zeuscs09/perch/firmware/main/pch_props.h

// Prop — ของที่มาสคอตถือหรือลอยเหนือหัว บอกว่ากำลังทำอะไร
// พอร์ตจาก tools/gen/props.py แบบตรงตัว (ตัวเลขต้องตรงกัน ไม่งั้น preview โกหก)
#pragma once

#include "pch_rects.h"

typedef enum {
    PCH_PROP_NONE = 0,
    PCH_PROP_MAGNIFIER,
    PCH_PROP_LAPTOP,
    PCH_PROP_HAMMER,
    PCH_PROP_GLOBE,
    PCH_PROP_DOTS,
    PCH_PROP_BANG,
    PCH_PROP_CLOCK,
    PCH_PROP_ZZZ,
    PCH_PROP_SPARKLE,
    PCH_PROP_CREW,
    PCH_PROP_BEACON,
} pch_prop_t;

#define PCH_HEAD_CX 8.0f  // กึ่งกลางลำตัวในแนวนอน
#define PCH_HAND_X 17.0f  // ขอบซ้ายของพื้นที่ prop ที่ถือ (แขนจบที่ 16.25)
#define PCH_HAND_Y 3.0f  // = ขอบบนของแขน (NUB_Y ใน pch_mascot.c)

// ตาข้างขวา — อยู่ที่นี่เพราะ prop บางชิ้น (แว่นขยาย) ต้องเล็งไปที่ตา
// pch_mascot.c ใช้ค่าชุดเดียวกันนี้ ไม่ต้องซิงก์สองที่
// ตากว้างหนึ่งช่องตาราง (1.5) อยู่ช่องที่ 6 ของลำตัวและต่ำจากยอดหัวหนึ่งช่อง — ตามภาพอ้างอิง
#define PCH_EYE_R 11.0f
#define PCH_EYE_Y 1.5f
#define PCH_EYE_S 1.5f
// ตาที่อยู่หลังเลนส์ต้องโตกว่าอีกข้าง ไม่งั้นวงแหวนอ่านเป็นแค่ห่วงคล้องหน้า ไม่ใช่แว่นขยาย
// pch_mascot.c เป็นคนวาดตาที่ขยายแล้ว (มันรู้ว่าตากำลังเป็นท่าไหน เช่นตอนกะพริบ)
#define PCH_EYE_MAG 2.0f

// แล็ปท็อป — วางหน้าลำตัว ไม่ใช่ช่อง prop ข้างตัว จึงมีค่าคงที่ชุดของตัวเอง
// ใหญ่เกือบเท่าลำตัว แต่แคบกว่าอยู่ราวข้างละ 1 unit — ช่องนั้นคือที่ที่ไหล่ยังโผล่ให้เห็น
// แขนที่โผล่ข้างฝาคือแขนเดิมของลำตัว (nub) ที่ขยับขึ้นลง — ไม่มีแขนวาดเพิ่มพาดหน้าฝา
#define PCH_LID_X 3.25f  // ลำตัวกิน 2..14 — เหลือไหล่โผล่ข้างละ 1.25
#define PCH_LID_W 9.5f
#define PCH_LID_Y 4.5f   // ขอบบนต่ำกว่าตา (จบที่ 3.0) — จอไม่บังหน้า
#define PCH_LID_H 6.2f
#define PCH_LAP_X 2.55f  // ฐาน — ยื่นออกกว่าฝาจอนิดเดียว จึงอ่านเป็นแล็ปท็อปไม่ใช่ป้าย
#define PCH_LAP_W 10.9f
#define PCH_LAP_Y 10.7f  // ฐานจบพอดีระดับฝ่าเท้า (12.0) — แล็ปท็อปบังขาหมดทั้งสี่
#define PCH_LAP_H 1.3f

// ฟองข้อความเหนือหัว — thinking
#define PCH_BUB_W 9.4f
#define PCH_BUB_H 3.9f

// เลนส์ยังต้องใหญ่กว่าหัวและล้นขึ้นไปด้านบนเหมือนเดิม แต่หัวแคบลงตอนแก้สัดส่วน
// 6.0 คือค่าที่รูในวง (4.5) ยังกินตาที่ขยายแล้ว (1.5 x 2 = 3.0) ได้สบาย
// ทั้งคู่ต้องลงตารางพิกเซล (ทวีคูณของ 0.25) รวมถึงมุมที่ตัด s/4 = 1.5 และ s/4 - t = 0.75
// ด้วย: กระจกกับวงแหวนไล่บันไดมุมคนละชุด ถ้าค่าไหนตกครึ่งพิกเซล บันไดจะเหลื่อมกัน
#define PCH_LENS_S 6.0f   // ขนาดเลนส์แว่นขยาย
#define PCH_LENS_T 0.75f  // ความหนาของขอบเลนส์

// แว่นตา — ท่านั่งพิมพ์ (writing) ไม่ใช่ pch_prop_t เพราะติดหน้าไปกับตา
// ต้องยุบและเลื่อนไปพร้อมตาทุกเฟรม (pch_mascot.c จึงวาดมันในชุดเดียวกับตา ไม่ใช่ชุด prop)
// ทุกค่าลงตาราง 0.25 unit (= 1 px) รวมมุมที่ตัด s/4 = 0.75 และ s/4 - t = 0.25
#define PCH_GLS_S 3.0f
#define PCH_GLS_T 0.5f
// ขาแว่นยาวเท่าที่พอไปจบพอดีขอบลำตัว (2.0 และ 14.0) — เลยออกไปจะอ่านเป็นเส้นลอยข้างหัว
#define PCH_GLS_TEMPLE 0.75f

// ค้อน + หมวกวิศวกร + แท่นเหล็ก — ทั้งชุดคือ prop เดียวกัน (Bash) จึงใช้ค่าคงที่ร่วมกัน
// หนึ่งลูปคือการทุบหนึ่งครั้งที่มีจังหวะเงื้อนำ ไม่ใช่ค้อนเด้งขึ้นลงสองรอบ:
// จังหวะเงื้อคือสิ่งที่ทำให้การกระแทกมีน้ำหนัก ถ้าตัดทิ้งจะเหลือแค่ของขยับไปมา
typedef enum { PCH_HAM_READY, PCH_HAM_WINDUP, PCH_HAM_STRIKE, PCH_HAM_RECOVER } pch_ham_stage_t;
// ขอบเขตของแต่ละท่าในลูป — ท่าฟาดสั้นที่สุด (สองเฟรม) เพราะการกระแทกต้องคม
#define PCH_HAM_T_WINDUP 0.25f
#define PCH_HAM_T_STRIKE 0.45f
#define PCH_HAM_T_RECOVER 0.62f

#define PCH_ANVIL_CX 20.0f  // กลางแท่น = ปลายทางที่หัวค้อนตกลงมา
#define PCH_ANVIL_TOP 9.5f  // ผิวบนของบล็อก = ก้นของชิ้นงานร้อน ทั้งตอนยุบและไม่ยุบ
#define PCH_HOT_UP_H 1.3f   // ชิ้นงานยุบลงราวครึ่งหนึ่งตอนโดนทุบ
#define PCH_HOT_DOWN_H 0.7f

#define PCH_HAM_HEAD_W 4.0f  // หัวค้อน
#define PCH_HAM_HEAD_H 2.4f
#define PCH_HAM_GRIP_W 1.4f  // ความหนาของด้าม
#define PCH_HAM_STEP 0.65f  // ระยะไล่ของบล็อกด้ามต่อชิ้น ทั้งสองแกน = ทแยง 45 องศาพอดี
#define PCH_HAM_BLK 1.4f  // ด้านของบล็อกด้าม — ใหญ่กว่า step จึงเหลื่อมกันเป็นเส้นทึบ
#define PCH_HAM_N 5  // จำนวนบล็อกด้าม

void pch_prop_build(pch_rects_t *out, pch_prop_t prop, float phase, bool connected);

// กระจกในเลนส์แว่นขยาย — ต้องวาดก่อนตา จึงแยกออกจาก pch_prop_build() ที่วาดหลังตา
void pch_prop_magnifier_glass(pch_rects_t *out, float phase, bool connected);

// แว่นตาคร่อมตาสองข้าง — วาดหลังตาในชุดเดียวกับตา จึงแยกออกจาก pch_prop_build()
void pch_prop_glasses(pch_rects_t *out, float eye_l, bool connected);

// แท่นเหล็กที่ค้อนทุบ — วางอยู่กับพื้น จึงแยกจาก pch_prop_build() ที่ถูกเลื่อนตามตัวมาสคอต
void pch_prop_hammer_anvil(pch_rects_t *out, float phase, bool connected);

// ท่าของการทุบในเฟรมนี้ — pch_mascot.c ใช้กำหนดท่าตัวมาสคอตให้ตรงจังหวะกับค้อน
pch_ham_stage_t pch_prop_hammer_stage(float phase);
