zeuscs09/perch/firmware/main/pch_face.h

// โหมดทดลอง — ใบหน้าที่ขยับปากตามความดังเสียง (พอร์ตจาก Berlin บนเว็บ)
//
// ตอบคำถามเดียว: **ปากที่ขยับตามเสียงดูดีพอบนจอ 2.8 นิ้วไหม** ก่อนจะลงเงินซื้อบอร์ด
// ที่มีไมค์กับ codec — ยังไม่มีระบบเสียงในโหมดนี้ ใช้เส้นความดังที่อัดไว้ล่วงหน้าแทน
//
// กลไกปากมาจาก frontend/js/avatar.js ของ Berlin ตรงๆ:
//     mouthScaleY = 0.25 + speechAmp * 3.6
//     speechAmp   = lerp(speechAmp, target, 0.24)
// ไม่มี viseme ไม่มีการวิเคราะห์เสียงพูด — ความสูงของช่องปากผูกกับความดังตัวเดียว
#pragma once

// วาดหน้าแล้ววนเล่นเส้นเสียงไปเรื่อยๆ ไม่คืนค่า
void pch_face_run(void);
