zeuscs09/perch/firmware/main/pch_face_env.h

// เส้นความดังจากเสียงพูดจริง (macOS say -v Kanya, ไทย) ที่ 30 fps
// สร้างด้วย tools/make_envelope.py — ฝังไว้เพื่อทดสอบการขยับปากโดยยังไม่ต้องมีระบบเสียง
#pragma once
#include <stdint.h>

#define PCH_ENV_FPS 30
#define PCH_ENV_LEN 181

static const uint8_t PCH_ENV[PCH_ENV_LEN] = {
      2,   2,   3,   4, 113, 160, 158, 157, 160, 139, 129,  73,   5,   0,  26,  96,
    169, 200, 198, 198, 178,  69,   0,  10,  16,  68, 141, 130, 126, 103,  52,   1,
      0,   0,   0,   0,   0,   9, 123, 149, 183, 196, 179, 207, 212, 214, 175, 136,
    201, 197, 195, 184, 115,   3,   0, 102, 159, 154, 159, 156, 214, 221, 213,  91,
     91, 147, 146, 140, 102,   6,   1,   7,   3,   2,  43, 179, 162, 146, 130, 117,
    122, 113, 118, 109, 105,  54,   5,   0,   0,   0,   0,   0,   0,  11,  18, 125,
    147, 139, 117,  35,   0,   0,  12,  26, 175, 198, 190, 176, 180, 243, 255, 250,
    240, 239, 232, 211, 192, 181, 175, 170, 164, 124,  26,   0,   0,   0,   0,   0,
      0, 116, 241, 253, 249, 248, 220, 145,  31,  86, 149, 136,  33, 103, 157, 152,
    147, 151, 173, 173, 146,  66, 108, 182, 178, 180, 174, 118,  31,  29,  21, 112,
    184, 192, 195, 186, 188, 206, 229, 225, 147, 134, 136,  89,   7,   3,   7,  27,
    128, 137, 127, 109,  70,
};
