zeuscs09/perch/firmware/main/pch_led.h

// RGB LED บนบอร์ด — ไฟบอกสถานะที่อ่านได้จากหางตา
//
// จอตอบว่า "เกิดอะไรขึ้นบ้าง" ซึ่งต้องหันไปอ่าน ส่วนไฟตอบคำถามเดียว:
// "ต้องลุกไปทำอะไรไหม" คำถามนั้นต้องตอบได้โดยไม่ต้องหันหน้า ไฟจึงไม่พยายาม
// บอกอะไรมากกว่าหนึ่งอย่าง
//
// ใช้ PWM ไม่ใช่เปิด/ปิดล้วน — เปิด/ปิดได้แค่ 7 สีและกะพริบแข็งๆ ซึ่งบนโต๊ะทำงาน
// อ่านเป็นสัญญาณเตือนตลอดเวลา ส่วนการหายใจช้าๆ อยู่ร่วมกับคนได้ทั้งวัน
#pragma once

#include <stdbool.h>

#include "pch_model.h"

void pch_led_init(void);

// กลางคืน = ดับสนิท ไม่ว่าสถานะจะเป็นอะไร
//
// เหตุผลที่ไฟดวงนี้มีอยู่คือ "บอกว่ามีคนรอเราตอบ" ซึ่งเป็นข้อความที่ส่งถึงคนที่ทำงานอยู่
// คนที่นอนอยู่ข้างๆ ไม่ได้เป็นผู้รับ ไฟส้มที่เต้นทุก 1.4 วินาทีข้างหัวเตียงจึงไม่ใช่
// สัญญาณอีกต่อไป มันคือสิ่งรบกวน
void pch_led_set_night(bool on);

// บอกไฟว่าภาพรวมตอนนี้เป็นยังไง — เรียกทุกครั้งที่ snapshot เปลี่ยน
// ไม่ต่อลิงก์ = ดับ (ไฟที่ยังสวยอยู่ตอนขาดการติดต่อคือการโกหก)
void pch_led_apply(const pch_snapshot_t *snap, bool connected);

// เดินจังหวะหายใจ เรียกจากลูปหลักพร้อมเวลาที่ผ่านไป (ms)
void pch_led_tick(int elapsed_ms);
