zeuscs09/perch/firmware/main/pch_night.h

// โหมดกลางคืน — จอเหลือแค่นาฬิกา ไฟดับ ไม่เตือนอะไรทั้งนั้น
//
// สำหรับเครื่องที่วางอยู่ในห้องนอน ซึ่งเปลี่ยนความหมายของทุกอย่างบนจอ:
// ตอนกลางวันมันคือแดชบอร์ดที่ควรเรียกร้องความสนใจเมื่อมีเรื่อง ตอนกลางคืนคนที่อยู่
// ในห้องไม่ได้จะลุกไปแก้อะไร การเตือนจึงไม่ได้ช่วยใคร มีแต่ปลุกคนให้ตื่น
//
// ## ทำไมถึงตัดทั้งจอ ไม่ใช่แค่หรี่ไฟหลัง
//
// จอ 320x240 ที่มีท้องฟ้าเต็มผืนกับมาสคอตสีชมพูสามตัว ปล่อยแสงออกมามากกว่าตัวเลข
// นาฬิกาบนพื้นดำหลายเท่า ต่อให้ไฟหลังเท่ากัน — ความสว่างที่ตาเห็นมาจาก *จำนวนพิกเซล
// ที่ติด* ไม่ใช่แค่กำลังไฟหลัง การหรี่อย่างเดียวจึงไม่พอสำหรับห้องมืด
#pragma once

#include <stdbool.h>

// เวลาปัจจุบันจาก snapshot ("HH:MM") — ตัวเดียวที่บอกบอร์ดว่าตอนนี้กี่โมง
// บอร์ดไม่มีนาฬิกาจริงของตัวเอง เวลาจึงมาพร้อมข้อมูลเสมอ
void pch_night_set_clock(const char *hhmm);

// ผู้ใช้แตะจอ — ออกจากโหมดกลางคืนชั่วคราว แล้วกลับเข้าเอง
void pch_night_wake(void);

void pch_night_tick(int elapsed_ms);

// อยู่ในโหมดกลางคืนอยู่ไหม (กลางคืน *และ* ไม่ได้เพิ่งถูกแตะ)
bool pch_night_active(void);
