zeuscs09/perch/firmware/main/pch_ui.c

#include "pch_ui.h"

#include <math.h>
#include <stdio.h>
#include <string.h>

#include "pch_mascot.h"
#include "pch_rects.h"
#include "layout.h"
#include "lvgl.h"

// ความสูง/ระยะของการ์ด — ตรงกับ tools/gen/screen.py
#define CARD_H 36
#define CARD_GAP 4

// หนึ่งลูปอนิเมชันยาวเท่าไร (ms) — ตรงกับสมมติฐาน "ลูปหนึ่งราว 1 วินาที" ของ mascot.c
#define LOOP_MS 1000
#define FRAME_MS 60

// นานแค่ไหนที่แผงโควตาค้างอยู่หลังถูกแตะ
//
// สั้นกว่านี้อ่านสี่ช่องไม่ทัน ยาวกว่านี้แล้วการ์ดที่รอการกระทำถูกบังนานเกินกว่าที่
// การถามครั้งเดียวควรได้ — แตะซ้ำต่อเวลาได้อยู่แล้ว
#define PCH_PEEK_MS 8000

typedef struct {
    lv_obj_t *canvas;  // ตัววาดมาสคอต (วาดเองใน LV_EVENT_DRAW_MAIN)
    lv_obj_t *label;   // ป้ายชื่อโปรเจกต์
    int index;
} slot_t;

typedef struct {
    lv_obj_t *box;
    lv_obj_t *accent;
    lv_obj_t *title;
    lv_obj_t *body;
} card_t;

typedef struct {
    lv_obj_t *percent;  // ตัวเลขใหญ่ — สิ่งเดียวที่ต้องอ่านออกจากอีกฝั่งห้อง
    // LVGL ไม่มี montserrat ตัวหนา — ซ้อนป้ายเดิมเยื้อง 1px แทน (เทียบเท่า
    // stroke_width=1 ของ Pillow ฝั่ง preview) ต้องอัปเดตข้อความ/สีคู่กันเสมอ
    lv_obj_t *percent_bold;
    lv_obj_t *pill;     // ป้ายบอกว่าเป็นหน้าต่างไหน สีคงที่ ไม่ตามระดับ
    lv_obj_t *pill_text;
    lv_obj_t *track;  // รางแถบ
    lv_obj_t *fill;   // เนื้อแถบ
    lv_obj_t *pace;   // ขีดบอกว่า "ควรใช้ถึงไหนแล้ว" ตามเวลาที่ผ่านไปในหน้าต่าง
    lv_obj_t *reset;  // countdown
} usage_row_t;

static pch_snapshot_t s_snap;
static bool s_connected = false;
// โหมดกลางคืน — ตัดทุกอย่างเหลือนาฬิกา (ดูเหตุผลใน pch_night.h)
static bool s_night = false;

// แถบโควตาย่อบน topbar — ตรงกับ tools/gen/screen.py:_topbar
#define USAGE_TOP_W 34
#define USAGE_TOP_H 6

// ทุกอย่างที่เกาะขอบขวาของแถบเริ่มนับจากตรงนี้ ไม่ใช่จากขอบจอ — ไอคอนลิงก์จองที่
// ขวาสุดไว้ถาวร ค่าคงที่ตัวเดียวจึงต้องเลื่อนนาฬิกา "+N" และแถบโควตาไปพร้อมกัน
#define TOPBAR_RIGHT (6 + PCH_TOPBAR_LINK_ICON_W + PCH_TOPBAR_LINK_ICON_GAP)

// ไอคอนลิงก์เป็นรายการสี่เหลี่ยมเหมือนของอื่นทั้งจอ ไม่ใช่ glyph จากฟอนต์ —
// ต้องตรงกับ tools/gen/screen.py:_link_icon เป๊ะทั้งพิกัดและสี
typedef struct {
    uint8_t x, y, w, h;
} icon_rect_t;

// BLE = แท่งไต่ขึ้น (ทางหลัก) · WiFi = คลื่นซ้อน (ทางสำรอง) · ขาด = ขีดเดียวจางๆ
// สามรูปทรงคนละวงศ์ ไม่ใช่รูปเดียวคนละสี — จอนี้ถูกมองจากอีกฝั่งห้องเป็นหลัก
static const icon_rect_t ICON_BLE[] = {{0, 6, 3, 3}, {4, 3, 3, 6}, {8, 0, 3, 9}};
static const icon_rect_t ICON_WIFI[] = {{0, 0, 11, 2}, {2, 3, 7, 2}, {4, 6, 3, 3}};
static const icon_rect_t ICON_NONE[] = {{1, 4, 9, 2}};
#define LINK_ICON_PARTS 3

// --- ฉากท้องฟ้า ---------------------------------------------------------------
// ฟ้า 22..93 แล้วพื้นดินลงไปถึงก้นจอ — วาดในผืนเดียวหลังทุกอย่าง
// ตรรกะทั้งหมดต้องตรงกับ tools/gen/sky.py
typedef enum {
    PCH_SKY_NIGHT = 0,
    PCH_SKY_DAWN,
    PCH_SKY_DAY,
    PCH_SKY_DUSK,
    PCH_SKY_PHASE_COUNT,
    PCH_SKY_NONE,  // ไม่ต่อลิงก์ หรือยังไม่รู้เวลา -> ไม่มีฉากเลย
} pch_sky_phase_t;

static const uint16_t SKY_BG[PCH_SKY_PHASE_COUNT] = {PCH_COL_SKY_NIGHT, PCH_COL_SKY_DAWN,
                                                    PCH_COL_SKY_DAY, PCH_COL_SKY_DUSK};
static const uint16_t SKY_GROUND[PCH_SKY_PHASE_COUNT] = {
    PCH_COL_GROUND_NIGHT, PCH_COL_GROUND_DAWN, PCH_COL_GROUND_DAY, PCH_COL_GROUND_DUSK};
static const uint16_t SKY_GRASS[PCH_SKY_PHASE_COUNT] = {
    PCH_COL_GRASS_NIGHT, PCH_COL_GRASS_DAWN, PCH_COL_GRASS_DAY, PCH_COL_GRASS_DUSK};
static const uint16_t SKY_SHADOW[PCH_SKY_PHASE_COUNT] = {
    PCH_COL_SHADOW_NIGHT, PCH_COL_SHADOW_DAWN, PCH_COL_SHADOW_DAY, PCH_COL_SHADOW_DUSK};
// กลางคืนไม่มีเมฆ ช่องแรกจึงไม่ถูกใช้
static const uint16_t SKY_CLOUD[PCH_SKY_PHASE_COUNT] = {0, PCH_COL_CLOUD_DAWN, PCH_COL_CLOUD_DAY,
                                                       PCH_COL_CLOUD_DUSK};

// เงาใต้เท้า — กว้าง 11 unit วางใต้เส้นขอบฟ้า ตรงกับ SHADOW_W ใน tools/gen/screen.py
#define SHADOW_W_UNIT 11.0f
#define SHADOW_H 5
// กึ่งกลางลำตัวในหน่วย unit (BODY = 1.0 กว้าง 14.0 ใน tools/gen/mascot.py)
#define BODY_CX 8.0f

static lv_obj_t *s_sky;
static pch_sky_phase_t s_sky_phase = PCH_SKY_NONE;
static float s_sky_hours = -1.0f;  // เวลาที่ใช้หาตำแหน่งดวง — <0 คือไม่รู้
static int s_cloud_shift = -1;     // เมฆเลื่อนไปกี่พิกเซลแล้ว ใช้ตัดสินว่าต้องวาดใหม่ไหม

static lv_obj_t *s_stroll;  // มาสคอตเดินข้ามจอตอนไม่มี session — กินแถบ slot ทั้งแถบ
static lv_obj_t *s_dot, *s_link, *s_clock_small, *s_overflow, *s_usage_top;
static lv_obj_t *s_link_icon[LINK_ICON_PARTS];
static lv_obj_t *s_usage_track, *s_usage_fill;
static lv_obj_t *s_clock_big, *s_date;
static lv_obj_t *s_card_more;  // "+N more" ใต้การ์ดใบล่างสุด
static slot_t s_slots[PCH_SLOTS_COUNT];
static card_t s_cards[PCH_MAX_CARDS];
static usage_row_t s_usage[PCH_USAGE_ROWS];

// เซลล์เครื่อง — สองบรรทัดเล็กในช่องที่ 4 ของตารางโควตา
// ตั้งใจให้หน้าตาไม่เหมือนแถวโควตา เพราะมันเป็นค่าคนละชนิด (ไม่มีเส้นตายรีเซ็ต)
// ถ้าทำให้เหมือนกัน ช่อง "resets in" ที่ว่างเปล่าจะอ่านเป็นข้อมูลขาด ไม่ใช่ดีไซน์
static struct {
    lv_obj_t *label[2];  // "CPU" / "RAM"
    lv_obj_t *value[2];
    lv_obj_t *track[2];
    lv_obj_t *fill[2];
} s_machine;
#define MACHINE_LINE_H 18
#define MACHINE_BAR_H 4
#define MACHINE_LABEL_W 30

static float s_phase = 0.0f;
static int s_cycle = 0;

// RGB565 -> สีของ LVGL (ขยายกลับเป็น 8 บิตต่อช่องแบบเดียวกับ quantize565 ฝั่ง Python)
static lv_color_t pch_color(uint16_t c)
{
    uint8_t r5 = (c >> 11) & 0x1F, g6 = (c >> 5) & 0x3F, b5 = c & 0x1F;
    return lv_color_make((r5 * 255 + 15) / 31, (g6 * 255 + 31) / 63, (b5 * 255 + 15) / 31);
}

// ขอบซ้ายของ slot ที่ i เมื่อกำลังแสดง session อยู่ n ตัว
// ระยะห่างคงที่ 80px เสมอ แต่ยกทั้งกลุ่มมาไว้กึ่งกลางจอ — สิ่งที่ต้องนิ่งคือ *ลำดับ*
static int slot_x(int i, int n)
{
    return (int)lroundf((PCH_SCREEN_WIDTH - n * PCH_SLOTS_WIDTH) / 2.0f) + i * PCH_SLOTS_WIDTH;
}

// "14:32" -> 14.533 · คืนค่าติดลบเมื่ออ่านไม่ได้
// ติดลบไม่ใช่เที่ยงคืน แต่คือ "ยังไม่รู้เวลา" — ตอนบูตก่อน sync ครั้งแรก clock เป็น "--:--"
// ต้องตกมาทางนี้ ไม่ใช่ไปโผล่เป็นฉากกลางดึก
static float pch_clock_hours(const char *c)
{
    for (int i = 0; i < 5; i++) {
        if (c[i] == '\0') return -1.0f;
    }
    if (c[2] != ':') return -1.0f;
    for (int i = 0; i < 5; i++) {
        if (i == 2) continue;
        if (c[i] < '0' || c[i] > '9') return -1.0f;
    }
    int h = (c[0] - '0') * 10 + (c[1] - '0');
    int m = (c[3] - '0') * 10 + (c[4] - '0');
    if (h > 23 || m > 59) return -1.0f;
    return (float)h + (float)m / 60.0f;
}

// ชั่วโมง -> ช่วง — กระโดดที่ขอบ ไม่ผสมสีระหว่างช่วง
static pch_sky_phase_t sky_phase_at(float t)
{
    if (t < PCH_SKY_DAWN_HOUR || t >= PCH_SKY_NIGHT_HOUR) return PCH_SKY_NIGHT;
    if (t < PCH_SKY_DAY_HOUR) return PCH_SKY_DAWN;
    if (t < PCH_SKY_DUSK_HOUR) return PCH_SKY_DAY;
    return PCH_SKY_DUSK;
}

// สัดส่วนของเส้นทาง (0..1) -> จุดกึ่งกลางดวงบนส่วนโค้ง
// ที่ u=0 และ u=1 ดวงอยู่บนเส้นขอบฟ้าพอดี (จมครึ่งดวง) ที่ขอบจอทั้งสองข้าง
static void sky_arc(float u, float *x, float *y)
{
    *x = -(float)PCH_SKY_ARC_PAD + u * (float)(PCH_SCREEN_WIDTH + 2 * PCH_SKY_ARC_PAD);
    *y = (float)PCH_SKY_HORIZON - sinf((float)M_PI * u) * (float)PCH_SKY_ARC_PEAK;
}

// ดวงอาทิตย์ 05:00->19:00 · ดวงจันทร์ 19:00->05:00 — มีดวงใดดวงหนึ่งบนฟ้าเสมอ
static void sky_disc(float t, float *x, float *y, uint16_t *color)
{
    if (t >= PCH_SKY_DAWN_HOUR && t < PCH_SKY_NIGHT_HOUR) {
        sky_arc((t - PCH_SKY_DAWN_HOUR) / (float)(PCH_SKY_NIGHT_HOUR - PCH_SKY_DAWN_HOUR), x, y);
        pch_sky_phase_t p = sky_phase_at(t);
        *color = (p == PCH_SKY_DAWN || p == PCH_SKY_DUSK) ? PCH_COL_SUN_LOW : PCH_COL_SUN;
        return;
    }
    float span = (float)(24 - PCH_SKY_NIGHT_HOUR + PCH_SKY_DAWN_HOUR);
    sky_arc(fmodf(t - PCH_SKY_NIGHT_HOUR + 24.0f, 24.0f) / span, x, y);
    *color = PCH_COL_MOON;
}

static void fill_rect(lv_layer_t *layer, int x0, int y0, int x1, int y1, uint16_t color,
                      int radius)
{
    if (x1 < x0 || y1 < y0) return;
    lv_draw_rect_dsc_t dsc;
    lv_draw_rect_dsc_init(&dsc);
    dsc.bg_opa = LV_OPA_COVER;
    dsc.border_width = 0;
    dsc.bg_color = pch_color(color);
    dsc.radius = radius;
    lv_area_t a = {.x1 = x0, .y1 = y0, .x2 = x1, .y2 = y1};
    lv_draw_rect(layer, &dsc, &a);
}

static void draw_stars(lv_layer_t *layer, pch_sky_phase_t phase)
{
    if (phase == PCH_SKY_DAY) return;
    // ดาวเป็นสี่เหลี่ยมอย่างน้อย star_px x star_px ทุกดวง — จุด 1px หายไปเลยบนแผงจริง
    const int d = PCH_SKY_STAR_PX - 1;
    if (phase != PCH_SKY_NIGHT) {
        // ฟ้ายังสว่างเกินกว่าจะเห็นทั้งหมด — ดวงแรกๆ สีหรี่ ไม่กะพริบ
        for (int i = 0; i < PCH_SKY_LOW_STAR_N; i++) {
            int x = pch_sky_stars[i][0], y = pch_sky_stars[i][1];
            fill_rect(layer, x, y, x + d, y + d, PCH_COL_STAR_DIM, 0);
        }
        return;
    }
    // ดวงที่กะพริบไล่สว่างขึ้นแล้วหรี่ลง: dim -> mid -> star(โต) -> mid ขั้นละ 1 วินาที
    // ตั้งต้นที่หรี่แล้วสว่างขึ้น ไม่ใช่ตั้งต้นสว่างแล้วดับ — ดาวดับอ่านเป็นจอเสีย
    // ขั้นสว่างสุดโตเป็น star_peak_px ด้วย: บนแผงจริงต่างแค่สีจางเกินกว่าจะจับได้
    // i * 3 ทำให้สี่ดวงเริ่มคนละขั้น (0,3,2,1) ไม่กะพริบพร้อมกันเป็นจังหวะเดียว
    static const uint16_t ramp[4] = {PCH_COL_STAR_DIM, PCH_COL_STAR_MID, PCH_COL_STAR,
                                     PCH_COL_STAR_MID};
    static const int ramp_px[4] = {PCH_SKY_STAR_PX, PCH_SKY_STAR_PX, PCH_SKY_STAR_PEAK_PX,
                                   PCH_SKY_STAR_PX};
    for (int i = 0; i < PCH_SKY_STARS_COUNT; i++) {
        int x = pch_sky_stars[i][0], y = pch_sky_stars[i][1];
        if (i >= PCH_SKY_TWINKLE_N) {
            fill_rect(layer, x, y, x + d, y + d, PCH_COL_STAR, 0);
            continue;
        }
        int step = (s_cycle + i * 3) % 4, s = ramp_px[step];
        // โตออกจากกึ่งกลาง ไม่ใช่ยืดลงขวา — ไม่งั้นดวงที่โตขึ้นอ่านเป็นดาวเลื่อนที่
        int off = (s - PCH_SKY_STAR_PX) / 2;
        fill_rect(layer, x - off, y - off, x - off + s - 1, y - off + s - 1, ramp[step], 0);
    }
}

// ประกาศล่วงหน้า — draw_clouds ต้องรู้ว่าฟ้าปิดอยู่ไหม แต่บล็อกอากาศอยู่ใต้มัน
static bool weather_is_covered(void);

static void draw_clouds(lv_layer_t *layer, pch_sky_phase_t phase, float t)
{
    uint16_t color = SKY_CLOUD[phase];
    // กลางคืนปกติไม่มีเมฆ (มองไม่เห็น) แต่ตอนฟ้าปิดต้องเห็น ไม่งั้นฝนตกลงมาจากฟ้าโล่ง
    if (phase == PCH_SKY_NIGHT) {
        if (!weather_is_covered()) return;
        color = PCH_COL_SKY_OVERCAST;
    }
    // ฟ้าปิดใช้ก้อนเพิ่ม โดยหาตำแหน่งของก้อนที่เกินตารางเดิมจากดัชนีของมันเอง
    int count = weather_is_covered() ? PCH_WEATHER_OVERCAST_CLOUDS : PCH_SKY_CLOUDS_COUNT;
    float span = (float)(PCH_SCREEN_WIDTH + 2 * PCH_SKY_CLOUD_PAD);
    for (int i = 0; i < count; i++) {
        bool extra = i >= PCH_SKY_CLOUDS_COUNT;
        float base_x = extra ? (float)((i * 83 + 29) % PCH_SCREEN_WIDTH) : pch_sky_clouds[i][0];
        int y = extra ? (34 + (i * 17) % 46) : pch_sky_clouds[i][1];
        int w = extra ? (30 + (i * 11) % 26) : pch_sky_clouds[i][2];
        float x = fmodf(base_x + t * (float)PCH_SKY_CLOUD_SPEED_PX_S, span) - PCH_SKY_CLOUD_PAD;
        int xi = (int)lroundf(x);
        fill_rect(layer, xi, y, xi + w, y + 9, color, 4);
        // ก้อนบนทำให้อ่านเป็นเมฆ ไม่ใช่แถบ — เยื้องซ้ายของกึ่งกลาง ไม่ใช่สมมาตร
        int bx = (int)lroundf(x + w * 0.2f), bw = (int)lroundf(w * 0.45f);
        fill_rect(layer, bx, y - 5, bx + bw, y + 4, color, 4);
    }
}

// กอหญ้างอกขึ้นจากเส้นขอบฟ้าไปในฟ้า — ก้านกลางสูงสุด ขนาบด้วยก้านสั้นสองข้าง
// งอกขึ้น ไม่ใช่ห้อยลง: หญ้าที่ยื่นลงไปในพื้นอ่านเป็นรอยขีดบนดิน ไม่ใช่ต้นไม้
static void draw_grass(lv_layer_t *layer, pch_sky_phase_t phase)
{
    uint16_t color = SKY_GRASS[phase];
    int y = PCH_SKY_HORIZON - 1;
    for (int i = 0; i < PCH_SKY_GRASS_X_COUNT; i++) {
        int x = pch_sky_grass_x[i];
        int main = 3 + i % 4, side = 2 + i % 3;  // สูงเท่ากันหมดอ่านเป็นรั้ว ไม่ใช่หญ้า
        // ก้านหนา 2px เว้นช่อง 1px — ก้าน 1px หายไปเลยบนแผงจริง
        fill_rect(layer, x, y - main, x + 1, y, color, 0);
        fill_rect(layer, x - 3, y - side, x - 2, y, color, 0);
        fill_rect(layer, x + 3, y - (2 + (side + 1) % 3), x + 4, y, color, 0);
    }
}


// ---- สภาพอากาศ ----------------------------------------------------------
//
// อากาศเป็น "อีกแกน" ของท้องฟ้า ไม่ใช่ phase ใหม่: เวลาของวันยังคุมความสว่างพื้นฐาน
// ส่วนอากาศคุมว่ามีอะไรบังฟ้าอยู่ ทั้งสองแกนต้องอ่านออกพร้อมกัน (ฝนตอนกลางคืน
// ต้องยังดูเป็นกลางคืน ไม่ใช่กลายเป็นสีเดียวกับฝนตอนบ่าย)

static bool weather_is_wet(void)
{
    if (!s_snap.has_weather) return false;
    return s_snap.weather == PCH_WEATHER_RAIN || s_snap.weather == PCH_WEATHER_STORM;
}

// ฟ้าปิดพอที่จะไม่เห็นดวงอาทิตย์/ดวงจันทร์และดาว
static bool weather_is_covered(void)
{
    if (!s_snap.has_weather) return false;
    return s_snap.weather != PCH_WEATHER_CLEAR;
}

// สีฟ้าหลังหักผลของอากาศ — กลางคืนไม่ถูกแทนที่ ฟ้าปิดตอนกลางคืนก็ยังมืดเหมือนเดิม
// (เมฆที่หนาขึ้นเป็นตัวบอกเองว่าปิด) ไม่งั้นฝนตอนตีสองจะสว่างกว่าฟ้าโปร่งตอนตีสอง
static uint16_t weather_sky_bg(pch_sky_phase_t phase)
{
    if (!s_snap.has_weather || phase == PCH_SKY_NIGHT) return SKY_BG[phase];
    switch (s_snap.weather) {
    case PCH_WEATHER_CLOUDY:
    case PCH_WEATHER_RAIN: return PCH_COL_SKY_OVERCAST;
    case PCH_WEATHER_STORM: return PCH_COL_SKY_STORM;
    case PCH_WEATHER_FOG: return PCH_COL_FOG;
    default: return SKY_BG[phase];
    }
}

// ฟ้าแลบ: กะพริบทั้งแผงสั้นๆ แล้วดับ — คำนวณจากเวลาล้วน ไม่เก็บสถานะ
static bool weather_flash_on(float t)
{
    if (!s_snap.has_weather || s_snap.weather != PCH_WEATHER_STORM) return false;
    return fmodf(t, PCH_WEATHER_FLASH_EVERY_S) < PCH_WEATHER_FLASH_HOLD_S;
}

// ฝนเป็นขีดเฉียงที่วนรอบเอง ไม่ใช่ particle จริง — ตำแหน่งแนวนอนกระจายด้วย
// ตัวคูณเฉพาะกิจให้ดูสุ่ม แต่คงที่ทุกครั้งที่บูต (ภาพนิ่งเวลาหยุดเวลา = ดีบักง่าย)
static void draw_rain(lv_layer_t *layer, float t)
{
    const int top = PCH_TOPBAR_HEIGHT;
    const int span = PCH_SKY_HORIZON - top;
    if (span <= 0) return;

    for (int i = 0; i < PCH_WEATHER_DROPS; i++) {
        int x0 = (i * 61 + 13) % PCH_SCREEN_WIDTH;
        // เหลื่อมเวลาเริ่มของแต่ละหยด ไม่งั้นตกเป็นแถวเดียวกันทั้งจอ
        float off = fmodf(t * PCH_WEATHER_DROP_SPEED_PX_S + (float)(i * 37 % span), (float)span);
        int y0 = top + (int)off;
        int y1 = y0 + PCH_WEATHER_DROP_LEN;
        if (y1 >= PCH_SKY_HORIZON) y1 = PCH_SKY_HORIZON - 1;
        if (y1 <= y0) continue;
        // เอียงด้วยการวาดทีละส่วน — เส้นเฉียงจริงแพงกว่าและมองไม่ออกที่ความยาว 7px
        int x1 = x0 + PCH_WEATHER_DROP_SLANT;
        fill_rect(layer, x0, y0, x0, (y0 + y1) / 2, PCH_COL_RAIN, 0);
        fill_rect(layer, x1, (y0 + y1) / 2, x1, y1, PCH_COL_RAIN, 0);
    }
}


// นาฬิกาตัวใหญ่สำหรับกลางคืน — วาดเองจากสี่เหลี่ยม ไม่ใช้ฟอนต์
//
// ฟอนต์ที่ใหญ่ที่สุดที่ LVGL มีมาให้คือ montserrat 48 ซึ่งเล็กเกินไปสำหรับจอที่ทั้งใบ
// มีแค่นาฬิกา การใส่ฟอนต์ใหญ่กว่านั้นต้องแปลงฟอนต์เองและกินแฟลชถาวรเพื่อหน้าจอเดียว
//
// ส่วนตัวเลขเจ็ดขีดวาดจากสี่เหลี่ยมได้ทุกขนาดโดยไม่กินแฟลชเพิ่มเลย — และเข้ากับภาษาภาพ
// ของทั้งเครื่องซึ่งประกอบจากสี่เหลี่ยมทั้งหมดอยู่แล้ว (มาสคอต ฟ้า แถบ) มันจึงไม่ใช่
// การประนีประนอม แต่เป็นตัวเลือกที่ตรงกว่าฟอนต์
#define BC_W 58   // กว้างต่อหลัก
#define BC_H 104  // สูง
#define BC_T 14   // ความหนาของขีด
#define BC_GAP 10
#define BC_COLON 14

// สีลำตัวมาสคอต ไม่ใช่สีข้อความปกติ
//
// สองเหตุผล และข้อหลังสำคัญกว่า: มันคือสีประจำเครื่องนี้ · และสีอุ่นมีองค์ประกอบ
// สีน้ำเงินน้อยกว่าสีขาวมาก ซึ่งเป็นช่วงคลื่นที่รบกวนการนอนมากที่สุด จอที่อยู่ในห้องนอน
// จึงควรเป็นสีนี้มากกว่าขาว แม้ความสว่างเท่ากัน
#define BC_COLOR PCH_COL_CLAY

// บิต: 0=บน 1=ขวาบน 2=ขวาล่าง 3=ล่าง 4=ซ้ายล่าง 5=ซ้ายบน 6=กลาง
static const uint8_t BC_SEG[10] = {0x3F, 0x06, 0x5B, 0x4F, 0x66, 0x6D, 0x7D, 0x07, 0x7F, 0x6F};

static void draw_digit(lv_layer_t *layer, int x, int y, int d, uint16_t col)
{
    if (d < 0 || d > 9) return;
    uint8_t m = BC_SEG[d];
    const int h = BC_T / 2, mid = y + (BC_H - BC_T) / 2;
    if (m & 0x01) fill_rect(layer, x + h, y, x + BC_W - 1 - h, y + BC_T - 1, col, 0);
    if (m & 0x40) fill_rect(layer, x + h, mid, x + BC_W - 1 - h, mid + BC_T - 1, col, 0);
    if (m & 0x08) fill_rect(layer, x + h, y + BC_H - BC_T, x + BC_W - 1 - h, y + BC_H - 1, col, 0);
    if (m & 0x20) fill_rect(layer, x, y + h, x + BC_T - 1, y + BC_H / 2 - 1, col, 0);
    if (m & 0x02) fill_rect(layer, x + BC_W - BC_T, y + h, x + BC_W - 1, y + BC_H / 2 - 1, col, 0);
    if (m & 0x10) fill_rect(layer, x, y + BC_H / 2, x + BC_T - 1, y + BC_H - 1 - h, col, 0);
    if (m & 0x04) fill_rect(layer, x + BC_W - BC_T, y + BC_H / 2, x + BC_W - 1, y + BC_H - 1 - h,
                            col, 0);
}

// วาด "HH:MM" กลางจอ — คืนขอบล่างไว้ให้คนวางบรรทัดวันที่ต่อ
static int draw_big_clock(lv_layer_t *layer, const char *hhmm)
{
    if (!hhmm || !hhmm[0]) return 0;
    int d[4] = {hhmm[0] - '0', hhmm[1] - '0', hhmm[3] - '0', hhmm[4] - '0'};

    int total = 4 * BC_W + 2 * BC_GAP + 2 * BC_GAP + BC_COLON;
    int x = (PCH_SCREEN_WIDTH - total) / 2;
    // กลางของพื้นที่ใต้แถบบน แล้วยกขึ้นเล็กน้อยเผื่อบรรทัดวันที่ข้างล่าง
    int y = PCH_TOPBAR_HEIGHT + (PCH_SCREEN_HEIGHT - PCH_TOPBAR_HEIGHT - BC_H) / 2 - 12;

    draw_digit(layer, x, y, d[0], BC_COLOR);
    x += BC_W + BC_GAP;
    draw_digit(layer, x, y, d[1], BC_COLOR);
    x += BC_W + BC_GAP;
    // จุดคู่ — สี่เหลี่ยมจัตุรัสสองอันที่หนึ่งในสามและสองในสามของความสูง
    int cy1 = y + BC_H / 3 - BC_T / 2, cy2 = y + 2 * BC_H / 3 - BC_T / 2;
    fill_rect(layer, x, cy1, x + BC_COLON - 1, cy1 + BC_T - 1, BC_COLOR, 0);
    fill_rect(layer, x, cy2, x + BC_COLON - 1, cy2 + BC_T - 1, BC_COLOR, 0);
    x += BC_COLON + BC_GAP;
    draw_digit(layer, x, y, d[2], BC_COLOR);
    x += BC_W + BC_GAP;
    draw_digit(layer, x, y, d[3], BC_COLOR);
    return y + BC_H;
}

static void sky_draw_cb(lv_event_t *e)
{
    lv_layer_t *layer = lv_event_get_layer(e);
    // กลางคืน: ผืนนี้เป็นของนาฬิกาทั้งหมด — ใช้ object เดิมเพราะมันกินพื้นที่ใต้แถบบน
    // พอดีอยู่แล้ว และมีวงจรวาดใหม่ของตัวเองที่ถูกต้องอยู่แล้ว
    if (s_night) {
        draw_big_clock(layer, s_snap.clock);
        return;
    }
    if (s_sky_phase == PCH_SKY_NONE) return;  // ไม่มีฉาก = ปล่อยให้เป็นพื้นจอเปล่า

    pch_sky_phase_t phase = s_sky_phase;
    float t = (float)s_cycle + s_phase;
    bool covered = weather_is_covered();

    // ฟ้าเริ่มใต้แถบบน ไม่ใช่ที่ขอบบนของแถบมาสคอต — แถบมาสคอตนั่งต่ำกว่านั้นลงมามาก
    uint16_t bg = weather_flash_on(t) ? PCH_COL_LIGHTNING : weather_sky_bg(phase);
    fill_rect(layer, 0, PCH_TOPBAR_HEIGHT, PCH_SCREEN_WIDTH - 1, PCH_SKY_HORIZON - 1, bg, 0);

    // ฟ้าปิด = ไม่เห็นดาวและไม่เห็นดวง ต้องหายไปพร้อมกัน ไม่งั้นอ่านเป็นฟ้าโปร่งสีแปลก
    if (!covered) {
        draw_stars(layer, phase);
        float x, y;
        uint16_t color;
        sky_disc(s_sky_hours, &x, &y, &color);
        int cx = (int)lroundf(x), cy = (int)lroundf(y), r = PCH_SKY_DISC_R;
        fill_rect(layer, cx - r, cy - r, cx + r, cy + r, color, LV_RADIUS_CIRCLE);
    }
    // หมอกคือฟ้าที่ไม่มีอะไรเลย — เมฆในหมอกมองไม่เห็นอยู่แล้ว
    if (!s_snap.has_weather || s_snap.weather != PCH_WEATHER_FOG) {
        draw_clouds(layer, phase, t);
    }
    if (weather_is_wet()) draw_rain(layer, t);

    // พื้นดินวาดทับหลังสุด — ครึ่งล่างของดวงและเมฆที่ต่ำเกินไปถูกตัดที่เส้นขอบฟ้าเอง
    fill_rect(layer, 0, PCH_SKY_HORIZON, PCH_SCREEN_WIDTH - 1, PCH_SCREEN_HEIGHT - 1,
              SKY_GROUND[phase], 0);
    draw_grass(layer, phase);
}

// เงาใต้เท้า — ปักหมุดว่าพื้นอยู่ตรงไหน ทำให้ท่ากระโดดอ่านเป็นกระโดด ไม่ใช่ลอย
// ขนาดคงที่ ไม่ยุบตามความสูงที่กระโดด
static void draw_shadow(lv_layer_t *layer, float body_cx)
{
    if (s_sky_phase == PCH_SKY_NONE) return;  // ไม่มีพื้นก็ไม่มีเงา
    float half = SHADOW_W_UNIT * PCH_SLOTS_UNIT_PX / 2.0f;
    fill_rect(layer, (int)lroundf(body_cx - half), PCH_SKY_HORIZON,
              (int)lroundf(body_cx + half), PCH_SKY_HORIZON + SHADOW_H - 1,
              SKY_SHADOW[s_sky_phase], LV_RADIUS_CIRCLE);
}

// --- การวาดมาสคอต ------------------------------------------------------------
static void draw_mascot_rects(lv_layer_t *layer, const pch_rects_t *rects, float ox, float oy)
{
    const float px = PCH_SLOTS_UNIT_PX;
    lv_draw_rect_dsc_t dsc;
    lv_draw_rect_dsc_init(&dsc);
    dsc.bg_opa = LV_OPA_COVER;
    dsc.border_width = 0;

    for (int i = 0; i < rects->count; i++) {
        const pch_rect_t *r = &rects->items[i];
        int x0 = (int)lroundf(ox + r->x * px);
        int y0 = (int)lroundf(oy + r->y * px);
        int x1 = (int)lroundf(ox + (r->x + r->w) * px);
        int y1 = (int)lroundf(oy + (r->y + r->h) * px);
        if (x1 <= x0 || y1 <= y0) continue;  // ชิ้นที่บางกว่าหนึ่งพิกเซลหายไปเลย
        // clamp เองแทนที่จะปล่อยให้ LVGL ทำ — ฝั่ง preview ใช้ PIL ซึ่งไม่ clamp ให้
        // ถ้าปล่อยไปคนละทาง ขาที่ยุบจนเตี้ยจะออกมาคนละรูปบนจอกับบน preview
        int radius = (int)lroundf(r->r * px);
        int half = ((x1 - x0) < (y1 - y0) ? (x1 - x0) : (y1 - y0)) / 2;
        dsc.radius = radius < half ? radius : half;
        dsc.bg_color = pch_color(r->color);
        lv_area_t a = {.x1 = x0, .y1 = y0, .x2 = x1 - 1, .y2 = y1 - 1};
        lv_draw_rect(layer, &dsc, &a);
    }
}

static void slot_draw_cb(lv_event_t *e)
{
    lv_obj_t *obj = lv_event_get_target_obj(e);
    slot_t *slot = (slot_t *)lv_obj_get_user_data(obj);
    if (!slot || slot->index >= s_snap.session_count) return;

    lv_layer_t *layer = lv_event_get_layer(e);
    lv_area_t coords;
    lv_obj_get_coords(obj, &coords);

    const float px = PCH_SLOTS_UNIT_PX;
    // ฝ่าเท้าอยู่เหนือขอบล่างของ slot เท่ากับ baseline_pad เสมอ ไม่ว่าท่าไหน
    float foot = coords.y1 + PCH_SLOTS_HEIGHT - PCH_SLOTS_BASELINE_PAD;
    float oy = foot - PCH_BOX_Y1 * px;
    float ox = coords.x1 + PCH_SLOTS_WIDTH / 2.0f - (PCH_BOX_X0 + PCH_BOX_X1) / 2.0f * px;

    // แต่ละตัวเดินคนละจังหวะเล็กน้อย ไม่งั้นดูเป็นหุ่นยนต์ชุดเดียวกัน
    float phase = fmodf(s_phase + slot->index * 0.17f, 1.0f);

    pch_state_t state = s_snap.sessions[slot->index].state;
    draw_shadow(layer, ox + (BODY_CX + pch_mascot_center_dx(state)) * px);

    pch_rects_t rects;
    // เอเจนต์ส่งเข้าไปตั้งแต่ build ไม่ใช่ทาสีทับทีหลัง — แต่ละตัวคนละรูปทรง จำนวนขาไม่เท่ากัน
    // และบางตัวมีจอ การแก้สีของ rect ที่วาดเสร็จแล้วเปลี่ยนรูปทรงไม่ได้
    pch_mascot_build_centered(&rects, state, phase, s_connected, s_cycle + slot->index,
                             s_snap.sessions[slot->index].agent);
    draw_mascot_rects(layer, &rects, ox, oy);
}

// ท่าที่หยุดทำกลางทาง วนไปตามรอบ — ต้องตรงกับ STROLL_ACTS ใน tools/gen/screen.py
static const pch_state_t STROLL_ACTS[] = {PCH_STATE_CELEBRATE, PCH_STATE_THINKING,
                                         PCH_STATE_SEARCHING, PCH_STATE_WAITING};
// ตำแหน่งหยุดเป็นสัดส่วนของเส้นทาง — วนคนละความยาวกับ ACTS เพื่อไม่ให้จับคู่ซ้ำ
static const float STROLL_PAUSE_AT[] = {0.34f, 0.5f, 0.66f};
#define STROLL_TRAVEL (PCH_SCREEN_WIDTH + 2 * PCH_STROLL_PAD_PX)

// เวลาสัมบูรณ์ (วินาที) -> ท่า + x ของขอบซ้ายกรอบวาด
// เที่ยวหนึ่ง = เดินจากนอกจอซ้ายไปนอกจอขวา โดยหยุดทำท่าหนึ่งครั้งกลางทาง
// ต้องตรงกับ stroll_pose ใน tools/gen/screen.py
static void stroll_pose(float t, pch_state_t *state, float *x)
{
    const float walk_s = (float)STROLL_TRAVEL / (float)PCH_STROLL_SPEED_PX_S;
    const float trip_s = walk_s + PCH_STROLL_PAUSE_S;
    int trip = (int)floorf(t / trip_s);
    float u = t - trip * trip_s;
    float hold_at = walk_s * STROLL_PAUSE_AT[trip % (int)(sizeof(STROLL_PAUSE_AT) /
                                                         sizeof(STROLL_PAUSE_AT[0]))];
    float walked;

    if (u < hold_at) {
        walked = u;
        *state = PCH_STATE_ENTERING;
    } else if (u < hold_at + PCH_STROLL_PAUSE_S) {
        walked = hold_at;
        *state = STROLL_ACTS[trip % (int)(sizeof(STROLL_ACTS) / sizeof(STROLL_ACTS[0]))];
    } else {
        walked = u - PCH_STROLL_PAUSE_S;
        *state = PCH_STATE_ENTERING;
    }
    *x = -(float)PCH_STROLL_PAD_PX + walked * PCH_STROLL_SPEED_PX_S;
}

static void stroll_draw_cb(lv_event_t *e)
{
    if (s_snap.session_count > 0) return;

    lv_obj_t *obj = lv_event_get_target_obj(e);
    lv_layer_t *layer = lv_event_get_layer(e);
    lv_area_t coords;
    lv_obj_get_coords(obj, &coords);

    pch_state_t state;
    float x;
    stroll_pose((float)s_cycle + s_phase, &state, &x);

    const float px = PCH_SLOTS_UNIT_PX;
    float foot = coords.y1 + PCH_SLOTS_HEIGHT - PCH_SLOTS_BASELINE_PAD;
    float ox = coords.x1 + x - PCH_BOX_X0 * px;

    // ตัวเดินเล่นใช้ build() ตรงๆ ไม่ผ่าน build_centered จึงไม่มี dx มาชดเชย
    draw_shadow(layer, ox + BODY_CX * px);

    pch_rects_t rects;
    // ตัวเดินเล่นตอนไม่มี session เป็น Claude เสมอ — ไม่มีเอเจนต์ไหนอ้างสิทธิ์ในฉากนี้
    // และมาสคอตส้มคือหน้าตาของโครงการเอง ไม่ใช่ตัวแทนของ session ใด session หนึ่ง
    pch_mascot_build(&rects, state, s_phase, s_connected, s_cycle, PCH_AGENT_CLAUDE);
    draw_mascot_rects(layer, &rects, ox, foot - PCH_BOX_Y1 * px);
}

// --- ตัวช่วยสร้าง widget ------------------------------------------------------
static lv_obj_t *plain_obj(lv_obj_t *parent, int w, int h)
{
    lv_obj_t *o = lv_obj_create(parent);
    lv_obj_remove_style_all(o);
    lv_obj_set_size(o, w, h);
    lv_obj_remove_flag(o, LV_OBJ_FLAG_SCROLLABLE);
    return o;
}

static lv_obj_t *plain_label(lv_obj_t *parent, const lv_font_t *font, uint16_t color)
{
    lv_obj_t *l = lv_label_create(parent);
    lv_obj_set_style_text_font(l, font, 0);
    lv_obj_set_style_text_color(l, pch_color(color), 0);
    lv_label_set_text(l, "");
    return l;
}

// ฉากอยู่หลังทุกอย่าง — ต้องสร้างก่อน widget อื่นทั้งหมด เพราะ LVGL เรียงชั้นตามลำดับสร้าง
// ผืนเดียวตั้งแต่ใต้แถบบนถึงก้นจอ: card วาดพื้นทึบของตัวเองทับอยู่แล้ว
static void build_sky(lv_obj_t *scr)
{
    s_sky = plain_obj(scr, PCH_SCREEN_WIDTH, PCH_SCREEN_HEIGHT - PCH_TOPBAR_HEIGHT);
    lv_obj_set_pos(s_sky, 0, PCH_TOPBAR_HEIGHT);
    lv_obj_add_event_cb(s_sky, sky_draw_cb, LV_EVENT_DRAW_MAIN, NULL);
}

// วาดฟ้าใหม่เฉพาะส่วนที่ขยับจริง — พื้นดินกับหญ้านิ่งตลอดช่วง ไม่ต้องแตะ
// แถบฟ้า 320x98 = 31360 px ซึ่งอยู่ในระดับเดียวกับที่แถบมาสคอตวาดใหม่ทุกเฟรม
// (28620 px) — วาดใหม่ไม่เกินวินาทีละครั้งหรือตอนเมฆขยับ (4 px/s) ไม่ใช่ทุกเฟรม
static void invalidate_sky_band(void)
{
    lv_area_t a = {.x1 = 0, .y1 = PCH_TOPBAR_HEIGHT, .x2 = PCH_SCREEN_WIDTH - 1,
                   .y2 = PCH_SKY_HORIZON - 1};
    lv_obj_invalidate_area(s_sky, &a);
}

// ช่วงเวลาเปลี่ยนเมื่อ clock เปลี่ยน (นาทีละครั้ง) หรือสถานะลิงก์เปลี่ยน
// ต้องวาดใหม่ทั้งผืนตอนช่วงเปลี่ยน เพราะพื้นดินกับหญ้าเปลี่ยนสีด้วย
static void update_sky(void)
{
    // กลางคืนผืนนี้เป็นนาฬิกา ไม่ใช่ฉาก — วงจรวาดใหม่ตามเฟสจึงไม่มีอะไรให้จับ
    // ต้องสั่งวาดเองตอนตัวเลขเปลี่ยน และ *เฉพาะ* ตอนนั้น: วาดทุกวินาทีคือการวาดใหม่
    // ทั้งผืน 320x218 หกสิบครั้งต่อนาทีเพื่อภาพที่เปลี่ยนครั้งเดียว
    if (s_night) {
        static char drawn[8];
        s_sky_phase = PCH_SKY_NONE;
        if (strncmp(drawn, s_snap.clock, sizeof(drawn) - 1) != 0) {
            snprintf(drawn, sizeof(drawn), "%s", s_snap.clock);
            lv_obj_invalidate(s_sky);
        }
        return;
    }

    pch_sky_phase_t was = s_sky_phase;
    // กลางคืนใช้ทางเดียวกับตอนหลุดลิงก์: ไม่มีเฟส = ไม่วาดฉากเลย
    //
    // ท้องฟ้ากับสนามหญ้ากินพื้นที่เกือบทั้งจอ มันคือแหล่งกำเนิดแสงที่ใหญ่ที่สุดของ
    // อุปกรณ์นี้ ต่อให้เป็นฟ้ากลางคืนที่สีเข้มแล้วก็ตาม — การหรี่ไฟหลังอย่างเดียว
    // ไม่ได้ลบพิกเซลที่ติดอยู่ออกไป
    float hours = (s_connected && !s_night) ? pch_clock_hours(s_snap.clock) : -1.0f;
    s_sky_hours = hours;
    s_sky_phase = hours < 0.0f ? PCH_SKY_NONE : sky_phase_at(hours);
    if (s_sky_phase != was) {
        lv_obj_invalidate(s_sky);
    } else if (s_sky_phase != PCH_SKY_NONE) {
        invalidate_sky_band();  // ดวงเลื่อนไปตามนาทีที่เดิน
    }
}

static void build_topbar(lv_obj_t *scr)
{
    lv_obj_t *bar = plain_obj(scr, PCH_SCREEN_WIDTH, PCH_TOPBAR_HEIGHT);
    lv_obj_set_pos(bar, 0, 0);
    lv_obj_set_style_bg_color(bar, pch_color(PCH_COL_BG_SLOT), 0);
    lv_obj_set_style_bg_opa(bar, LV_OPA_COVER, 0);

    s_dot = plain_obj(bar, 6, 6);
    lv_obj_set_pos(s_dot, 6, PCH_TOPBAR_HEIGHT / 2 - 3);
    lv_obj_set_style_bg_opa(s_dot, LV_OPA_COVER, 0);

    s_link = plain_label(bar, &lv_font_montserrat_12, PCH_COL_TEXT);
    lv_obj_align(s_link, LV_ALIGN_LEFT_MID, 17, 0);

    // ไอคอนลิงก์: สามชิ้นพอสำหรับทุกรูปทรง ชิ้นที่เกินก็ซ่อนไป — สร้างครั้งเดียวแล้ว
    // ขยับ ไม่ใช่สร้าง/ลบทุกครั้งที่ลิงก์เปลี่ยน ซึ่งบนจอที่กะพริบอยู่แล้วจะเห็นเป็นสะดุด
    for (int i = 0; i < LINK_ICON_PARTS; i++) {
        s_link_icon[i] = plain_obj(bar, 1, 1);
        lv_obj_set_style_bg_opa(s_link_icon[i], LV_OPA_COVER, 0);
        lv_obj_add_flag(s_link_icon[i], LV_OBJ_FLAG_HIDDEN);
    }

    s_clock_small = plain_label(bar, &lv_font_montserrat_12, PCH_COL_TEXT);
    lv_obj_align(s_clock_small, LV_ALIGN_RIGHT_MID, -TOPBAR_RIGHT, 0);

    s_overflow = plain_label(bar, &lv_font_montserrat_12, PCH_COL_ACCENT);
    lv_obj_align(s_overflow, LV_ALIGN_RIGHT_MID, -(TOPBAR_RIGHT + 38), 0);

    // โควตาย่อบนแถบ — โผล่เฉพาะตอนการ์ดยึดพื้นที่ล่างไป
    // ไม่มีป้ายกำกับ ("5h") เพราะบนแถบมีค่าเดียว ไม่ต้องบอกว่าตัวไหน
    // เอาพื้นที่นั้นไปทำแถบสั้นแทน ซึ่งเหลือบแล้วรู้ทันทีโดยไม่ต้องอ่านตัวเลข
    s_usage_top = plain_label(bar, &lv_font_montserrat_12, PCH_COL_GOOD);
    lv_obj_add_flag(s_usage_top, LV_OBJ_FLAG_HIDDEN);

    // กรอบขาวรอบราง — พื้นรางสีเดียวกับพื้นหลังจอ ทำให้ส่วนที่ยังไม่ถูกใช้กลืนหาย
    // เห็นแต่ "ใช้ไปเท่าไร" ไม่เห็น "เหลือเท่าไร" กรอบตีขอบให้รู้ความยาวเต็ม
    s_usage_track = plain_obj(bar, USAGE_TOP_W + 2, USAGE_TOP_H + 2);
    lv_obj_set_style_bg_color(s_usage_track, pch_color(PCH_COL_BG), 0);
    lv_obj_set_style_bg_opa(s_usage_track, LV_OPA_COVER, 0);
    lv_obj_set_style_border_width(s_usage_track, 1, 0);
    lv_obj_set_style_border_color(s_usage_track, pch_color(PCH_COL_OUTLINE), 0);
    lv_obj_set_style_border_opa(s_usage_track, LV_OPA_COVER, 0);
    lv_obj_add_flag(s_usage_track, LV_OBJ_FLAG_HIDDEN);

    s_usage_fill = plain_obj(s_usage_track, USAGE_TOP_W, USAGE_TOP_H);
    lv_obj_set_style_bg_opa(s_usage_fill, LV_OPA_COVER, 0);
    lv_obj_set_pos(s_usage_fill, 0, 0);
}

static void build_slots(lv_obj_t *scr)
{
    for (int i = 0; i < PCH_SLOTS_COUNT; i++) {
        s_slots[i].index = i;
        lv_obj_t *o = plain_obj(scr, PCH_SLOTS_WIDTH, PCH_SLOTS_HEIGHT);
        lv_obj_set_pos(o, slot_x(i, PCH_SLOTS_COUNT), PCH_SLOTS_TOP);
        lv_obj_set_user_data(o, &s_slots[i]);
        lv_obj_add_event_cb(o, slot_draw_cb, LV_EVENT_DRAW_MAIN, NULL);
        s_slots[i].canvas = o;

        lv_obj_t *l = plain_label(scr, &lv_font_montserrat_12, PCH_COL_TEXT);
        lv_obj_set_width(l, PCH_SLOTS_WIDTH - 4);
        lv_obj_set_style_text_align(l, LV_TEXT_ALIGN_CENTER, 0);
        lv_label_set_long_mode(l, LV_LABEL_LONG_DOT);
        s_slots[i].label = l;
    }
}

// แถบ slot ที่ว่างเปล่าอ่านได้ว่า "อุปกรณ์ค้าง" — ให้มาสคอตเดินผ่านแทน
// ผืนเดียวเต็มความกว้างจอ ไม่ใช่ slot เพราะตัวนี้ข้ามขอบ slot ตลอดเวลา
static void build_stroll(lv_obj_t *scr)
{
    s_stroll = plain_obj(scr, PCH_SCREEN_WIDTH, PCH_SLOTS_HEIGHT);
    lv_obj_set_pos(s_stroll, 0, PCH_SLOTS_TOP);
    lv_obj_add_event_cb(s_stroll, stroll_draw_cb, LV_EVENT_DRAW_MAIN, NULL);
    lv_obj_add_flag(s_stroll, LV_OBJ_FLAG_HIDDEN);
}

static void build_cards(lv_obj_t *scr)
{
    int w = PCH_SCREEN_WIDTH - PCH_CARD_PAD * 2;
    for (int i = 0; i < PCH_MAX_CARDS; i++) {
        lv_obj_t *box = plain_obj(scr, w, CARD_H);
        lv_obj_set_pos(box, PCH_CARD_PAD, PCH_CARD_TOP + PCH_CARD_PAD + i * (CARD_H + CARD_GAP));
        lv_obj_set_style_bg_color(box, pch_color(PCH_COL_BG_SLOT), 0);
        lv_obj_set_style_bg_opa(box, LV_OPA_COVER, 0);

        lv_obj_t *accent = plain_obj(box, 3, CARD_H);
        lv_obj_set_pos(accent, 0, 0);
        lv_obj_set_style_bg_opa(accent, LV_OPA_COVER, 0);

        lv_obj_t *title = plain_label(box, &lv_font_montserrat_14, PCH_COL_TEXT);
        lv_obj_set_width(title, w - 18);
        lv_label_set_long_mode(title, LV_LABEL_LONG_DOT);
        lv_obj_set_pos(title, 9, 4);

        lv_obj_t *body = plain_label(box, &lv_font_montserrat_12, PCH_COL_TEXT_DIM);
        lv_obj_set_width(body, w - 18);
        lv_label_set_long_mode(body, LV_LABEL_LONG_DOT);
        lv_obj_set_pos(body, 9, 20);

        s_cards[i] = (card_t){box, accent, title, body};
        lv_obj_add_flag(box, LV_OBJ_FLAG_HIDDEN);
    }

    // ตำแหน่งแนวตั้งขึ้นกับจำนวนใบที่แสดงจริง — ตั้งตอน layout_cards ไม่ใช่ตรงนี้
    s_card_more = plain_label(scr, &lv_font_montserrat_12, PCH_COL_TEXT_DIM);
    lv_obj_add_flag(s_card_more, LV_OBJ_FLAG_HIDDEN);
}

// ขอบซ้าย/ขวาของเนื้อหาในแถว usage — ตรงกับ tools/gen/screen.py:_usage_row
#define USAGE_X0 (PCH_CARD_PAD + 8)
#define USAGE_X1 (PCH_SCREEN_WIDTH - PCH_CARD_PAD - 8)
#define USAGE_W (USAGE_X1 - USAGE_X0)

// ป้ายของแต่ละช่อง — สองช่องแรกเป็นของ Claude จึงไม่ต้องเขียนชื่อกำกับ
// ช่องที่ 4 สำรองไว้ ยังไม่มี daemon ตัวไหนส่งค่ามาให้ (ถูกซ่อนอยู่)
static const char *const USAGE_LABELS[PCH_USAGE_ROWS] = {"Current", "Weekly", "Codex", "—"};
static const int USAGE_WINDOWS[PCH_USAGE_ROWS] = {PCH_USAGE_SESSION_WINDOW,
                                                 PCH_USAGE_WEEKLY_WINDOW,
                                                 PCH_USAGE_WEEKLY_WINDOW,
                                                 PCH_USAGE_WEEKLY_WINDOW};
// สี pill — สองช่องแรกคงสีเดิมของ Claude ช่องของ Codex ใช้สีลำตัวมาสคอตตัวเดียวกัน
// เพื่อให้แถบกับมาสคอตบนจอเดียวกันอ่านเป็นของเจ้าเดียวกัน
static const uint16_t USAGE_PILL_COLORS[PCH_USAGE_ROWS] = {PCH_COL_CLAY, PCH_COL_GOOD,
                                                          PCH_COL_CODEX, PCH_COL_ANTIGRAV};

// จำนวนแถวจริงของตาราง — ปัดขึ้นเผื่อช่องสุดท้ายไม่เต็มคอลัมน์
#define USAGE_GRID_ROWS ((PCH_USAGE_ROWS + PCH_USAGE_COLS - 1) / PCH_USAGE_COLS)
// ความกว้างของหนึ่งช่อง หลังหักช่องไฟระหว่างคอลัมน์
#define USAGE_CELL_W ((USAGE_W - (PCH_USAGE_COLS - 1) * PCH_USAGE_GUTTER) / PCH_USAGE_COLS)
// pill แคบลงจาก 62 เพราะช่องแคบลงครึ่งหนึ่ง — ยังพอใส่ "Current" ที่ฟอนต์ 12
#define USAGE_PILL_W 50

// ช่อง i เรียงตามแถวก่อน (0,1 = แถวบน / 2,3 = แถวล่าง) — คู่ของ Claude จึงอยู่บรรทัด
// เดียวกัน ซึ่งเป็นคู่ที่ต้องอ่านเทียบกันบ่อยที่สุด
// ต้องตรงกับ _usage ใน tools/gen/screen.py
static int usage_row_y(int i)
{
    int block = USAGE_GRID_ROWS * PCH_USAGE_ROW_H + (USAGE_GRID_ROWS - 1) * PCH_USAGE_GAP;
    int row = i / PCH_USAGE_COLS;
    return PCH_CARD_TOP + (PCH_CARD_HEIGHT - block) / 2 + row * (PCH_USAGE_ROW_H + PCH_USAGE_GAP);
}

static int usage_cell_x(int i)
{
    return USAGE_X0 + (i % PCH_USAGE_COLS) * (USAGE_CELL_W + PCH_USAGE_GUTTER);
}

static void build_usage(lv_obj_t *scr)
{
    for (int i = 0; i < PCH_USAGE_ROWS; i++) {
        int y = usage_row_y(i);
        int x = usage_cell_x(i);
        usage_row_t *u = &s_usage[i];

        u->percent_bold = plain_label(scr, &lv_font_montserrat_24, PCH_COL_GOOD);
        lv_obj_set_pos(u->percent_bold, x + 1, y + 1);
        u->percent = plain_label(scr, &lv_font_montserrat_24, PCH_COL_GOOD);
        lv_obj_set_pos(u->percent, x, y);

        // pill วาดด้วย obj โค้งมุม ไม่ใช่ label ที่มีพื้นหลัง เพราะต้องกำหนดความกว้าง
        // จากความยาวข้อความเองตอน build (ข้อความคงที่ ไม่เปลี่ยนตามข้อมูล)
        u->pill = plain_obj(scr, USAGE_PILL_W, 18);
        lv_obj_set_style_bg_color(u->pill, pch_color(USAGE_PILL_COLORS[i]), 0);
        lv_obj_set_style_bg_opa(u->pill, LV_OPA_COVER, 0);
        lv_obj_set_style_radius(u->pill, 9, 0);
        lv_obj_set_pos(u->pill, x + USAGE_CELL_W - USAGE_PILL_W, y + 5);

        // ตัวอักษรสีหมึกบนพื้น pill สว่าง — สีข้อความเดิมจมกับพื้นส้ม/เขียว
        u->pill_text = plain_label(u->pill, &lv_font_montserrat_12, PCH_COL_INK);
        lv_label_set_text(u->pill_text, USAGE_LABELS[i]);
        lv_obj_center(u->pill_text);

        // รางต้องสว่างกว่าพื้นจอพอให้เห็นความยาวเต็มของแถบตอนใช้ไปน้อย
        u->track = plain_obj(scr, USAGE_CELL_W, PCH_USAGE_BAR_H);
        lv_obj_set_style_bg_color(u->track, pch_color(PCH_COL_GRAY_DARK), 0);
        lv_obj_set_style_bg_opa(u->track, LV_OPA_COVER, 0);
        lv_obj_set_style_radius(u->track, LV_RADIUS_CIRCLE, 0);
        lv_obj_set_pos(u->track, x, y + 28);

        u->fill = plain_obj(u->track, USAGE_CELL_W, PCH_USAGE_BAR_H);
        lv_obj_set_style_bg_opa(u->fill, LV_OPA_COVER, 0);
        lv_obj_set_style_radius(u->fill, LV_RADIUS_CIRCLE, 0);
        lv_obj_set_pos(u->fill, 0, 0);

        u->pace = plain_obj(scr, 1, PCH_USAGE_BAR_H + 4);
        lv_obj_set_style_bg_color(u->pace, pch_color(PCH_COL_OUTLINE), 0);
        lv_obj_set_style_bg_opa(u->pace, LV_OPA_COVER, 0);
        lv_obj_set_pos(u->pace, x, y + 26);

        // เวลารีเซ็ตอยู่บรรทัดเดียวกับเลข % ไม่ใช่ชั้นใต้แถบ — ประหยัด 16px ต่อแถว
        // โดยไม่ต้องลดขนาดเลข %
        //
        // เกาะขอบขวาของป้ายเลข % ไม่ใช่พิกัดตายตัวที่กันที่ไว้ให้ "100%" ซึ่งทำให้
        // เลขสองหลักดูห่างจนไม่เป็นก้อนเดียวกัน ตำแหน่งจริงคำนวณใน layout_usage
        // หลังตั้งข้อความ — lv_obj_align_to คิดครั้งเดียวตอนเรียก ไม่ตามความกว้างใหม่เอง
        u->reset = plain_label(scr, &lv_font_montserrat_12, PCH_COL_TEXT_DIM);

        lv_obj_add_flag(u->percent, LV_OBJ_FLAG_HIDDEN);
        lv_obj_add_flag(u->percent_bold, LV_OBJ_FLAG_HIDDEN);
        lv_obj_add_flag(u->pill, LV_OBJ_FLAG_HIDDEN);
        lv_obj_add_flag(u->track, LV_OBJ_FLAG_HIDDEN);
        lv_obj_add_flag(u->pace, LV_OBJ_FLAG_HIDDEN);
        lv_obj_add_flag(u->reset, LV_OBJ_FLAG_HIDDEN);
    }
}

// ช่องที่ 4 ของตาราง (แถวล่าง คอลัมน์ขวา) — ที่เดียวกับที่ usage row 3 จะไปอยู่
// ทั้งคู่ไม่เคยโผล่พร้อมกัน: daemon ส่ง usage มาแค่ 3 ช่อง ช่องที่ 4 จึงว่างเสมอ
static void build_machine(lv_obj_t *scr)
{
    int x = usage_cell_x(3);
    int y = usage_row_y(3);
    for (int i = 0; i < 2; i++) {
        int ly = y + i * MACHINE_LINE_H;

        s_machine.label[i] = plain_label(scr, &lv_font_montserrat_12, PCH_COL_TEXT_DIM);
        lv_label_set_text(s_machine.label[i], i == 0 ? "CPU" : "RAM");
        lv_obj_set_pos(s_machine.label[i], x, ly);

        s_machine.value[i] = plain_label(scr, &lv_font_montserrat_12, PCH_COL_TEXT);
        lv_obj_set_pos(s_machine.value[i], x + MACHINE_LABEL_W, ly);

        s_machine.track[i] = plain_obj(scr, USAGE_CELL_W - MACHINE_LABEL_W - 34, MACHINE_BAR_H);
        lv_obj_set_style_bg_color(s_machine.track[i], pch_color(PCH_COL_GRAY_DARK), 0);
        lv_obj_set_style_bg_opa(s_machine.track[i], LV_OPA_COVER, 0);
        lv_obj_set_style_radius(s_machine.track[i], LV_RADIUS_CIRCLE, 0);
        lv_obj_set_pos(s_machine.track[i], x + MACHINE_LABEL_W + 34, ly + 5);

        s_machine.fill[i] = plain_obj(s_machine.track[i], 1, MACHINE_BAR_H);
        lv_obj_set_style_bg_opa(s_machine.fill[i], LV_OPA_COVER, 0);
        lv_obj_set_style_radius(s_machine.fill[i], LV_RADIUS_CIRCLE, 0);
        lv_obj_set_pos(s_machine.fill[i], 0, 0);

        lv_obj_add_flag(s_machine.label[i], LV_OBJ_FLAG_HIDDEN);
        lv_obj_add_flag(s_machine.value[i], LV_OBJ_FLAG_HIDDEN);
        lv_obj_add_flag(s_machine.track[i], LV_OBJ_FLAG_HIDDEN);
    }
}

static void build_idle_clock(lv_obj_t *scr)
{
    // ไม่มีอะไรต้องเตือน = ให้พื้นที่นี้ทำหน้าที่นาฬิกาตั้งโต๊ะแทน
    // นี่คือสภาพที่จอเป็นอยู่เกือบตลอดเวลา ปล่อยว่างแล้วดูเหมือนอุปกรณ์พัง
    int cy = PCH_CARD_TOP + PCH_CARD_HEIGHT / 2;
    s_clock_big = plain_label(scr, &lv_font_montserrat_48, PCH_COL_TEXT);
    lv_obj_align(s_clock_big, LV_ALIGN_TOP_MID, 0, cy - 8 - 24);
    s_date = plain_label(scr, &lv_font_montserrat_12, PCH_COL_TEXT_DIM);
    lv_obj_align(s_date, LV_ALIGN_TOP_MID, 0, cy + 26 - 8);
}

void pch_ui_init(void)
{
    pch_model_clear(&s_snap);

    lv_obj_t *scr = lv_screen_active();
    lv_obj_remove_style_all(scr);
    lv_obj_set_style_bg_color(scr, pch_color(PCH_COL_BG), 0);
    lv_obj_set_style_bg_opa(scr, LV_OPA_COVER, 0);
    lv_obj_remove_flag(scr, LV_OBJ_FLAG_SCROLLABLE);

    build_sky(scr);
    build_topbar(scr);
    build_slots(scr);
    build_stroll(scr);
    build_cards(scr);
    build_usage(scr);
    build_machine(scr);
    build_idle_clock(scr);
    pch_ui_set_snapshot(&s_snap);
}

// --- ปรับหน้าจอตาม snapshot ---------------------------------------------------
static void layout_slots(void)
{
    // กลางคืนไม่มีตัวละครบนจอเลย ทั้งมาสคอตประจำ session และตัวที่เดินเล่นตอนว่าง —
    // สามตัวนี้เป็นพื้นที่สว่างก้อนใหญ่ที่สุดบนจอ และเป็นสิ่งที่ขยับตลอดเวลาด้วย
    int n = s_night ? 0 : s_snap.session_count;
    if (n == 0 && !s_night) {
        lv_obj_remove_flag(s_stroll, LV_OBJ_FLAG_HIDDEN);
    } else {
        lv_obj_add_flag(s_stroll, LV_OBJ_FLAG_HIDDEN);
    }
    for (int i = 0; i < PCH_SLOTS_COUNT; i++) {
        slot_t *s = &s_slots[i];
        if (i >= n) {
            lv_obj_add_flag(s->canvas, LV_OBJ_FLAG_HIDDEN);
            lv_obj_add_flag(s->label, LV_OBJ_FLAG_HIDDEN);
            continue;
        }
        int x = slot_x(i, n);
        lv_obj_remove_flag(s->canvas, LV_OBJ_FLAG_HIDDEN);
        lv_obj_remove_flag(s->label, LV_OBJ_FLAG_HIDDEN);
        lv_obj_set_pos(s->canvas, x, PCH_SLOTS_TOP);

        lv_label_set_text(s->label, s_snap.sessions[i].project);
        lv_obj_set_style_text_color(
            s->label, pch_color(s_connected ? PCH_COL_TEXT : PCH_COL_TEXT_DIM), 0);
        int foot = PCH_SLOTS_TOP + PCH_SLOTS_HEIGHT - PCH_SLOTS_BASELINE_PAD;
        lv_obj_set_pos(s->label, x + 2, foot + 4);
    }
}

static uint16_t card_accent(pch_card_kind_t kind)
{
    switch (kind) {
        case PCH_CARD_ALERT: return PCH_COL_ALERT;
        case PCH_CARD_DONE: return PCH_COL_GOOD;
        default: return PCH_COL_ACCENT;
    }
}

// นับถอยหลังของการขอดูโควตา — ศูนย์คือกลับไปให้การ์ดครองพื้นที่ตามเดิม
static int s_peek_ms = 0;


// ทั้งการ์ดและโควตามาจาก host ทั้งคู่ ลิงก์หลุดแล้วไม่มีใครรับรองว่ายังจริง — พื้นที่ล่าง
// จึงว่างทั้งแถบและตกเป็นของนาฬิกา ตรงกับ Screen.shown_{cards,usage}() ใน gen/screen.py
static int shown_card_count(void)
{
    // ระหว่างที่ผู้ใช้ขอดูโควตา ให้ถือว่าไม่มีการ์ด — การ์ดกับแผงโควตาแย่งพื้นที่เดียวกัน
    // และการ์ดชนะเสมอเพราะมันคือสิ่งที่ต้องการการกระทำ แต่ "ต้องการการกระทำ" กับ
    // "ผู้ใช้กำลังเอานิ้วจิ้มถามอยู่เดี๋ยวนี้" อันหลังชนะ
    if (s_peek_ms > 0) return 0;
    // กลางคืนไม่มีการ์ด — คนที่นอนอยู่ในห้องไม่ได้จะลุกไปแก้อะไร การเตือนจึงไม่ได้
    // ช่วยใคร มีแต่ปลุกให้ตื่น (เรื่องที่ค้างยังอยู่ครบ รอให้แตะดูตอนเช้า)
    if (s_night) return 0;
    return s_connected ? s_snap.card_count : 0;
}

static bool usage_shown(void)
{
    if (s_night) return false;
    return s_snap.has_usage && s_connected;
}

static void layout_cards(void)
{
    int n = shown_card_count();
    for (int i = 0; i < PCH_MAX_CARDS; i++) {
        if (i >= n) {
            lv_obj_add_flag(s_cards[i].box, LV_OBJ_FLAG_HIDDEN);
            continue;
        }
        const pch_card_t *c = &s_snap.cards[i];
        lv_obj_remove_flag(s_cards[i].box, LV_OBJ_FLAG_HIDDEN);
        lv_obj_set_style_bg_color(s_cards[i].accent, pch_color(card_accent(c->kind)), 0);
        lv_label_set_text(s_cards[i].title, c->title);
        lv_label_set_text(s_cards[i].body, c->body);
    }

    // การ์ดที่ไม่ได้วาดต้องเหลือร่องรอย ไม่ใช่หายเงียบ — "ไม่มีอะไรค้างแล้ว" กับ
    // "ยังค้างอีกสองเรื่องแต่จอไม่พอ" คือสองสถานะที่ต้องแยกออกได้ในเหลือบเดียว
    if (n > 0 && s_snap.card_overflow > 0) {
        // ตัดที่ 99 — เกินกว่านั้นตัวเลขที่แน่นอนไม่ได้บอกอะไรเพิ่มแล้ว มีแต่จะล้นบรรทัด
        int more = s_snap.card_overflow > 99 ? 99 : s_snap.card_overflow;
        char buf[16];
        snprintf(buf, sizeof(buf), "+%d more", more);
        lv_label_set_text(s_card_more, buf);
        int y = PCH_CARD_TOP + PCH_CARD_PAD + n * (CARD_H + CARD_GAP) + 1;
        lv_obj_align(s_card_more, LV_ALIGN_TOP_RIGHT, -(PCH_CARD_PAD + 8), y);
        lv_obj_remove_flag(s_card_more, LV_OBJ_FLAG_HIDDEN);
    } else {
        lv_obj_add_flag(s_card_more, LV_OBJ_FLAG_HIDDEN);
    }

    // พื้นที่ล่างมีผู้ยึดสองราย (การ์ด, โควตา) — ถ้ามีรายใดรายหนึ่ง นาฬิกาใหญ่ต้องหลบ
    // ขึ้นไปอยู่บนแถบ ไม่งั้นนาฬิกาหายจากจอทั้งใบ หรือโผล่ซ้ำสองที่
    bool taken = n > 0 || usage_shown();
    if (taken) {
        lv_obj_add_flag(s_clock_big, LV_OBJ_FLAG_HIDDEN);
        lv_obj_add_flag(s_date, LV_OBJ_FLAG_HIDDEN);
        lv_obj_remove_flag(s_clock_small, LV_OBJ_FLAG_HIDDEN);
    } else if (s_night) {
        // กลางคืนวาดตัวเลขเองใน sky_draw_cb — ป้ายตัวเดิมต้องหลบ ไม่งั้นซ้อนกันสองชั้น
        lv_obj_add_flag(s_clock_big, LV_OBJ_FLAG_HIDDEN);
        lv_obj_add_flag(s_clock_small, LV_OBJ_FLAG_HIDDEN);
        lv_obj_remove_flag(s_date, LV_OBJ_FLAG_HIDDEN);
    } else {
        lv_obj_remove_flag(s_clock_big, LV_OBJ_FLAG_HIDDEN);
        lv_obj_remove_flag(s_date, LV_OBJ_FLAG_HIDDEN);
        lv_obj_add_flag(s_clock_small, LV_OBJ_FLAG_HIDDEN);
    }
}

static uint16_t usage_color(int percent)
{
    if (percent < 0) return PCH_COL_TEXT_DIM;
    if (percent >= PCH_USAGE_CRIT_PCT) return PCH_COL_ALERT;
    if (percent >= PCH_USAGE_WARN_PCT) return PCH_COL_ACCENT;
    return PCH_COL_GOOD;
}

// สีของแถบ — แดงทันทีที่ใช้เร็วกว่าเวลาที่ผ่านไปในหน้าต่าง ไม่ต้องรอถึงเกณฑ์ %
// "60% ตอนเหลือเวลาอีกครึ่ง" เป็นปัญหาคนละแบบกับ "60% ตอนหมดเวลาพอดี"
// ต้องตรงกับ usage_bar_color ใน tools/gen/screen.py
// และ MenuBadge.alarming ใน host/Sources/PerchCore/MenuBadge.swift (แถบเมนูใช้สูตร pace เดียวกัน แต่ไม่มีเกณฑ์ %)
static uint16_t usage_bar_color(const pch_usage_t *u, int window)
{
    if (u->percent < 0) return PCH_COL_TEXT_DIM;
    if (u->remaining > 0 && window > 0) {
        int elapsed = window - u->remaining;
        if (elapsed < 0) elapsed = 0;
        if (elapsed > window) elapsed = window;
        if ((int64_t)u->percent * window > (int64_t)elapsed * 100) return PCH_COL_ALERT;
    }
    return usage_color(u->percent);
}

// วินาทีที่เหลือ -> ข้อความสั้นที่สุดที่ยังบอกได้ว่าควรรีบไหม
// ต้องตรงกับ fmt_remaining ใน tools/gen/screen.py
//
// `terse` = ตัดหน่วยเล็กทิ้ง ใช้ตอนที่ยาวเต็มใส่ไม่ลง — "4d" ยังตอบว่าอีกนานไหม
// ส่วน "4d…" ตอบไม่ได้อะไรเลยนอกจากบอกว่าจอแคบ
static void usage_reset_text(const pch_usage_t *u, char *out, size_t cap, bool terse)
{
    // ช่องที่เหลือหลังหักเลข % กับ pill เหลือราว 40px ที่ฟอนต์ 12 — ราว 6 ตัวอักษร
    // ทุกคำในนี้จึงถูกเลือกให้สั้นกว่านั้น ไม่ใช่ให้อ่านลื่นที่สุด
    if (u->remaining < 0) {
        snprintf(out, cap, "no eta");
    } else if (u->remaining == 0) {
        snprintf(out, cap, "reset");
    } else {
        int d = u->remaining / 86400;
        int h = (u->remaining % 86400) / 3600;
        int m = (u->remaining % 3600) / 60;
        // ไม่มีคำว่า "Resets in" — ในตาราง 2 คอลัมน์ช่องกว้างครึ่งเดียว ข้อความเต็ม
        // (~90px) ล้นไปทับ pill ส่วน pill ก็บอกอยู่แล้วว่ากำลังอ่านหน้าต่างไหน
        if (d) {
            terse ? snprintf(out, cap, "%dd", d) : snprintf(out, cap, "%dd%dh", d, h);
        } else if (h) {
            terse ? snprintf(out, cap, "%dh", h) : snprintf(out, cap, "%dh%02dm", h, m);
        } else {
            snprintf(out, cap, "%dm", m);
        }
    }
}

// เลือกข้อความที่ยาวที่สุดที่ยังใส่ลงในที่ว่างจริง
//
// วัดเอา ไม่ใช่คำนวณจากจำนวนตัวอักษร — ความกว้างของเลข % เปลี่ยนตามค่า ("--%" กับ
// "100%" ต่างกันหลายพิกเซล) และฟอนต์ไม่ได้กว้างเท่ากันทุกตัว การเดาเคยพลาดมาแล้ว
// จนค่าปกติอย่าง "4d22h" โดนตัดเหลือ "4d…" ทั้งที่ไม่มีอะไรทับกันเลย
static void set_reset_text(lv_obj_t *label, const pch_usage_t *u, int avail)
{
    char buf[24];
    for (int terse = 0; terse <= 1; terse++) {
        usage_reset_text(u, buf, sizeof(buf), terse);
        lv_point_t size;
        lv_text_get_size(&size, buf, &lv_font_montserrat_12, 0, 0, LV_COORD_MAX,
                         LV_TEXT_FLAG_NONE);
        if (size.x <= avail) break;
    }
    lv_label_set_text(label, buf);
}

// โควตาย่อบนแถบตอนการ์ดยึดพื้นที่ล่าง — แสดงเฉพาะหน้าต่าง 5 ชม. ซึ่งเป็นตัวที่ขยับ
// เร็วพอจะเปลี่ยนการตัดสินใจภายในวันเดียว ส่วน weekly รอดูตอนการ์ดหายไปได้
static void layout_usage_topbar(void)
{
    bool show = usage_shown() && shown_card_count() > 0;
    if (!show) {
        lv_obj_add_flag(s_usage_top, LV_OBJ_FLAG_HIDDEN);
        lv_obj_add_flag(s_usage_track, LV_OBJ_FLAG_HIDDEN);
        return;
    }
    const pch_usage_t *u = &s_snap.usage[0];
    uint16_t col = usage_color(u->percent);

    if (u->percent < 0) {
        lv_label_set_text(s_usage_top, "--%");
    } else {
        lv_label_set_text_fmt(s_usage_top, "%d%%", u->percent);
    }
    lv_obj_set_style_text_color(s_usage_top, pch_color(col), 0);

    // หลบ "+N" เมื่อมันโผล่ ไม่งั้นทับกัน
    int right = -(TOPBAR_RIGHT + 38 + (s_snap.overflow > 0 ? 26 : 0));
    lv_obj_align(s_usage_top, LV_ALIGN_RIGHT_MID, right, 0);
    // align จัดที่ *ขอบขวา* ของ track ให้เอง — ไม่ต้องหักความกว้างแถบออกอีก
    // (ฝั่ง Pillow ต้องหักเองเพราะวาดจากมุมซ้ายบน) ตรงกับ tools/gen/screen.py:_topbar
    lv_obj_align(s_usage_track, LV_ALIGN_RIGHT_MID, right - 30, 0);

    if (u->percent < 0) {
        lv_obj_add_flag(s_usage_fill, LV_OBJ_FLAG_HIDDEN);
    } else {
        int pct = u->percent > 100 ? 100 : (u->percent < 0 ? 0 : u->percent);
        int w = (USAGE_TOP_W * pct + 50) / 100;
        if (w <= 0) {
            lv_obj_add_flag(s_usage_fill, LV_OBJ_FLAG_HIDDEN);
        } else {
            lv_obj_remove_flag(s_usage_fill, LV_OBJ_FLAG_HIDDEN);
            lv_obj_set_width(s_usage_fill, w);
            lv_obj_set_style_bg_color(s_usage_fill, pch_color(col), 0);
        }
    }
    lv_obj_remove_flag(s_usage_top, LV_OBJ_FLAG_HIDDEN);
    lv_obj_remove_flag(s_usage_track, LV_OBJ_FLAG_HIDDEN);
}

static void layout_machine(void)
{
    // ตามแผงโควตาเสมอ — การ์ดชนะทั้งคู่ ด้วยเหตุผลเดียวกัน
    bool show = s_snap.has_machine && usage_shown() && shown_card_count() == 0;
    int pct[2] = {s_snap.cpu_pct, s_snap.mem_pct};
    int track_w = USAGE_CELL_W - MACHINE_LABEL_W - 34;

    for (int i = 0; i < 2; i++) {
        if (!show) {
            lv_obj_add_flag(s_machine.label[i], LV_OBJ_FLAG_HIDDEN);
            lv_obj_add_flag(s_machine.value[i], LV_OBJ_FLAG_HIDDEN);
            lv_obj_add_flag(s_machine.track[i], LV_OBJ_FLAG_HIDDEN);
            continue;
        }
        int v = pct[i] < 0 ? 0 : (pct[i] > 100 ? 100 : pct[i]);
        // ใช้เกณฑ์สีชุดเดียวกับโควตา — ผู้ใช้เรียนรู้ครั้งเดียวใช้ได้ทั้งจอ
        uint16_t col = v >= PCH_USAGE_CRIT_PCT ? PCH_COL_ALERT
                     : v >= PCH_USAGE_WARN_PCT ? PCH_COL_ACCENT
                                              : PCH_COL_GOOD;
        lv_label_set_text_fmt(s_machine.value[i], "%d%%", v);
        lv_obj_set_style_text_color(s_machine.value[i], pch_color(col), 0);
        lv_obj_set_width(s_machine.fill[i], track_w * v / 100 > 0 ? track_w * v / 100 : 1);
        lv_obj_set_style_bg_color(s_machine.fill[i], pch_color(col), 0);

        lv_obj_remove_flag(s_machine.label[i], LV_OBJ_FLAG_HIDDEN);
        lv_obj_remove_flag(s_machine.value[i], LV_OBJ_FLAG_HIDDEN);
        lv_obj_remove_flag(s_machine.track[i], LV_OBJ_FLAG_HIDDEN);
    }
}

static void layout_usage(void)
{
    // การ์ดชนะโควตาเสมอ — การ์ดคือสิ่งที่ต้องการการกระทำจากผู้ใช้
    bool show = usage_shown() && shown_card_count() == 0;
    for (int i = 0; i < PCH_USAGE_ROWS; i++) {
        usage_row_t *row = &s_usage[i];
        if (!show) {
            lv_obj_add_flag(row->percent, LV_OBJ_FLAG_HIDDEN);
            lv_obj_add_flag(row->percent_bold, LV_OBJ_FLAG_HIDDEN);
            lv_obj_add_flag(row->pill, LV_OBJ_FLAG_HIDDEN);
            lv_obj_add_flag(row->track, LV_OBJ_FLAG_HIDDEN);
            lv_obj_add_flag(row->pace, LV_OBJ_FLAG_HIDDEN);
            lv_obj_add_flag(row->reset, LV_OBJ_FLAG_HIDDEN);
            continue;
        }
        const pch_usage_t *u = &s_snap.usage[i];
        // ไม่มีทั้งเปอร์เซ็นต์และเวลา = daemon ไม่เคยส่งช่องนี้มาเลย (เช่นช่องสำรอง)
        // ต่างจาก "รู้ว่ามีหน้าต่างแต่ยังไม่รู้ค่า" ซึ่งต้องโชว์ -- ตามดีไซน์เดิม
        if (u->percent == PCH_USAGE_UNKNOWN && u->remaining == PCH_USAGE_UNKNOWN) {
            lv_obj_add_flag(row->percent, LV_OBJ_FLAG_HIDDEN);
            lv_obj_add_flag(row->percent_bold, LV_OBJ_FLAG_HIDDEN);
            lv_obj_add_flag(row->pill, LV_OBJ_FLAG_HIDDEN);
            lv_obj_add_flag(row->track, LV_OBJ_FLAG_HIDDEN);
            lv_obj_add_flag(row->pace, LV_OBJ_FLAG_HIDDEN);
            lv_obj_add_flag(row->reset, LV_OBJ_FLAG_HIDDEN);
            continue;
        }
        uint16_t col = usage_bar_color(u, USAGE_WINDOWS[i]);

        lv_obj_remove_flag(row->percent, LV_OBJ_FLAG_HIDDEN);
        lv_obj_remove_flag(row->percent_bold, LV_OBJ_FLAG_HIDDEN);
        lv_obj_remove_flag(row->pill, LV_OBJ_FLAG_HIDDEN);
        lv_obj_remove_flag(row->track, LV_OBJ_FLAG_HIDDEN);
        lv_obj_remove_flag(row->reset, LV_OBJ_FLAG_HIDDEN);

        if (u->percent < 0) {
            lv_label_set_text(row->percent, "--%");
            lv_label_set_text(row->percent_bold, "--%");
        } else {
            lv_label_set_text_fmt(row->percent, "%d%%", u->percent);
            lv_label_set_text_fmt(row->percent_bold, "%d%%", u->percent);
        }
        lv_obj_set_style_text_color(row->percent, pch_color(col), 0);
        lv_obj_set_style_text_color(row->percent_bold, pch_color(col), 0);

        // เปอร์เซ็นต์ที่ไม่รู้ = แถบว่าง ไม่ใช่แถบศูนย์ที่ดูเหมือนข้อมูลจริง
        int pct = u->percent;
        if (pct < 0) pct = 0;
        if (pct > 100) pct = 100;
        int w = (USAGE_CELL_W * pct + 50) / 100;
        if (u->percent < 0 || w <= 0) {
            lv_obj_add_flag(row->fill, LV_OBJ_FLAG_HIDDEN);
        } else {
            lv_obj_remove_flag(row->fill, LV_OBJ_FLAG_HIDDEN);
            lv_obj_set_width(row->fill, w);
            lv_obj_set_style_bg_color(row->fill, pch_color(col), 0);
        }

        // ขีด pace หาได้จากเวลาที่เหลือล้วนๆ — ความยาวหน้าต่างเป็นค่าคงที่
        // ไม่ต้องส่งอะไรเพิ่มบนสาย และเดินต่อได้เองตอน BLE หลุด
        if (u->remaining > 0) {
            int elapsed = USAGE_WINDOWS[i] - u->remaining;
            if (elapsed < 0) elapsed = 0;
            if (elapsed > USAGE_WINDOWS[i]) elapsed = USAGE_WINDOWS[i];
            int y = usage_row_y(i) + 26;
            lv_obj_set_pos(row->pace,
                           usage_cell_x(i)
                               + (int)((int64_t)USAGE_CELL_W * elapsed / USAGE_WINDOWS[i]),
                           y);
            lv_obj_remove_flag(row->pace, LV_OBJ_FLAG_HIDDEN);
        } else {
            lv_obj_add_flag(row->pace, LV_OBJ_FLAG_HIDDEN);
        }

        // ความกว้างของป้ายเลข % เพิ่งเปลี่ยนตามข้อความ ("100%" กว้างกว่า "35%" ~13px)
        // ต้องบังคับให้ LVGL คิดขนาดใหม่ก่อน ไม่งั้นจัดชิดกับความกว้างของเฟรมก่อนหน้า
        lv_obj_update_layout(row->percent);

        // เพดานความกว้างของข้อความเวลา — ไม่ใช่การเผื่อ แต่เป็นการรับประกัน
        //
        // ป้ายนี้เกาะขอบขวาของเลข % ซึ่งกว้างไม่เท่ากันในแต่ละค่า ส่วน pill อยู่ชิดขอบขวา
        // ของช่องตายตัว ระยะที่เหลือจึงเปลี่ยนไปตามข้อมูล การเลือกคำให้สั้นพอจึงเป็นการ
        // เดาที่ถูกได้เฉพาะกับคำที่มีอยู่วันนี้ — เคยล้นมาแล้วสองครั้ง ("Resets in ..."
        // และ "resetting") ทั้งที่ครั้งแรกก็แก้ด้วยการย่อคำเหมือนกัน
        //
        // ตัดด้วยจุดไข่ปลาเมื่อไม่พอ ดีกว่าทับ pill: ข้อความที่อ่านไม่ครบยังบอกว่ามีอะไรอยู่
        // ส่วนตัวอักษรที่ซ้อนกันอ่านไม่ออกทั้งคู่
        int gap = 4;
        int avail = USAGE_CELL_W - USAGE_PILL_W - lv_obj_get_width(row->percent) - gap;
        if (avail < 0) avail = 0;
        set_reset_text(row->reset, u, avail);
        // จุดไข่ปลาเป็นด่านสุดท้าย ไม่ใช่ด่านแรก — ถึงตรงนี้ข้อความถูกย่อให้พอดีแล้ว
        // เหลือไว้เผื่อค่าที่ยาวเกินคาดจริงๆ เพราะทับ pill แย่กว่าอ่านไม่ครบ
        lv_obj_set_width(row->reset, avail);
        lv_label_set_long_mode(row->reset, LV_LABEL_LONG_DOT);
        lv_obj_align_to(row->reset, row->percent, LV_ALIGN_OUT_RIGHT_MID, gap, 0);
    }
}

// ประกาศล่วงหน้า — นาฬิกาใหญ่ถูกจัดตำแหน่งทั้งตอน snapshot มาถึงและตอนสลับโหมด
// กลางคืน แต่ตัวจริงต้องอยู่ใกล้ pch_ui_set_night ซึ่งเป็นเจ้าของสถานะโหมด
static void place_idle_clock(void);

// ประกาศล่วงหน้า — ป้ายลิงก์ถูกวาดใหม่ทั้งตอนลิงก์เปลี่ยนและตอน snapshot มาถึง
// แต่ตัวจริงต้องอยู่ใต้ pch_ui_set_link ซึ่งเป็นเจ้าของสถานะลิงก์
static void apply_link_label(void);

void pch_ui_set_snapshot(const pch_snapshot_t *snap)
{
    s_snap = *snap;

    apply_link_label();
    lv_label_set_text(s_clock_big, s_snap.clock);
    lv_label_set_text(s_clock_small, s_snap.clock);
    lv_label_set_text(s_date, s_snap.date);
    place_idle_clock();

    if (s_snap.overflow > 0) {
        lv_label_set_text_fmt(s_overflow, "+%d", s_snap.overflow);
        lv_obj_remove_flag(s_overflow, LV_OBJ_FLAG_HIDDEN);
    } else {
        lv_obj_add_flag(s_overflow, LV_OBJ_FLAG_HIDDEN);
    }

    update_sky();
    layout_slots();
    layout_cards();
    layout_usage();
    layout_machine();
    layout_usage_topbar();
}

// จำสถานะลิงก์ล่าสุดไว้ — ป้ายขึ้นกับทั้งลิงก์ *และ* ชื่อสถานที่ใน snapshot
// ซึ่งมาคนละจังหวะกัน ตัวไหนมาทีหลังก็ต้องวาดป้ายใหม่ได้เองโดยไม่ต้องรออีกตัว
static bool s_link_ble, s_link_wifi;
static char s_link_ip[40];

static void apply_link_label(void)
{
    const char *label = "no link";
    if (s_link_ble) {
        // ชื่อสถานที่ชนะชื่อบอร์ด: ตอนต่อติดแล้ว "ต่อกับอะไรอยู่" ไม่ใช่คำถามอีกต่อไป
        // (ไอคอนข้างๆ ตอบให้แล้ว) พื้นที่ตรงนี้จึงมีค่ากว่าถ้าบอกอย่างอื่น
        label = s_snap.place[0] ? s_snap.place : "perch";
    } else if (s_link_wifi && s_link_ip[0]) {
        label = s_link_ip;
    }

    // อุณหภูมิเกาะไปกับชื่อสถานที่ ไม่ใช่ไปอยู่ใต้นาฬิกาใหญ่
    //
    // ใต้นาฬิกาคือพื้นที่เดียวกับแผงโควตา ซึ่งโผล่อยู่เกือบตลอดเวลา อุณหภูมิที่วางไว้
    // ตรงนั้นจึงแทบไม่มีวันได้เห็น ส่วนแถบบนว่างอยู่แล้วและเห็นตลอด — แถมสถานที่
    // กับอากาศของที่นั่นเป็นเรื่องเดียวกัน วางคู่กันจึงอ่านเป็นก้อนเดียว
    if (s_link_ble && s_snap.has_weather && s_snap.temperature != PCH_TEMP_UNKNOWN) {
        static char line[PCH_PLACE_LEN + 10];
        snprintf(line, sizeof(line), "%s  %d\u00b0", label, s_snap.temperature);
        lv_label_set_text(s_link, line);
        return;
    }
    lv_label_set_text(s_link, label);
}

void pch_ui_set_link(bool ble, bool wifi, const char *ip)
{
    const icon_rect_t *parts = ICON_NONE;
    int count = 1;
    uint16_t col = PCH_COL_TEXT_DIM;
    if (ble) {
        parts = ICON_BLE;
        count = 3;
        col = PCH_COL_GOOD;
    } else if (wifi) {
        parts = ICON_WIFI;
        count = 3;
        col = PCH_COL_ACCENT;
    }

    // ป้ายข้างจุดพูดเรื่องเดียวกับไอคอน แต่ตอบคำถามที่ไอคอนตอบไม่ได้: "แล้วจะไปหามัน
    // ที่ไหน" — Mac ที่หาบอร์ดไม่เจอผ่าน mDNS ต้องการเลขนี้ และนั่นคือตอนที่ BLE ตายพอดี
    // (ตรงกับ _topbar ใน tools/gen/screen.py)
    s_link_ble = ble;
    s_link_wifi = wifi;
    s_link_ip[0] = '\0';
    if (ip) {
        strncpy(s_link_ip, ip, sizeof(s_link_ip) - 1);
        s_link_ip[sizeof(s_link_ip) - 1] = '\0';
    }
    apply_link_label();

    const int x0 = PCH_SCREEN_WIDTH - 6 - PCH_TOPBAR_LINK_ICON_W;
    const int y0 = (PCH_TOPBAR_HEIGHT - PCH_TOPBAR_LINK_ICON_H) / 2;
    for (int i = 0; i < LINK_ICON_PARTS; i++) {
        if (i >= count) {
            lv_obj_add_flag(s_link_icon[i], LV_OBJ_FLAG_HIDDEN);
            continue;
        }
        lv_obj_set_size(s_link_icon[i], parts[i].w, parts[i].h);
        lv_obj_set_pos(s_link_icon[i], x0 + parts[i].x, y0 + parts[i].y);
        lv_obj_set_style_bg_color(s_link_icon[i], pch_color(col), 0);
        lv_obj_remove_flag(s_link_icon[i], LV_OBJ_FLAG_HIDDEN);
    }
}

void pch_ui_set_connected(bool connected)
{
    if (connected == s_connected) return;
    s_connected = connected;
    lv_obj_set_style_bg_color(s_dot, pch_color(connected ? PCH_COL_GOOD : PCH_COL_GRAY), 0);
    // ข้อความของป้ายเป็นของ `pch_ui_set_link` (มันรู้ว่าทางไหนใช้อยู่และ IP คืออะไร)
    // ที่นี่เหลือแค่สี ซึ่งตอบคนละคำถาม: ตัวเลขบนจอยังสดอยู่ไหม
    lv_obj_set_style_text_color(s_link,
                                pch_color(connected ? PCH_COL_TEXT : PCH_COL_TEXT_DIM), 0);
    // นาฬิกาใหญ่หรี่เป็นเทาตอนหลุด — เวลาที่ค้างอยู่ยังอ่านได้ แต่ต้องไม่อ่านว่าเป็นตอนนี้
    // (ตรงกับ _idle_clock ใน tools/gen/screen.py)
    lv_obj_set_style_text_color(s_clock_big, pch_color(connected ? PCH_COL_TEXT : PCH_COL_GRAY), 0);
    update_sky();  // หลุดลิงก์ = ฉากหายทั้งผืน clock ที่ค้างอยู่ไม่ใช่เวลาจริงอีกต่อไป
    layout_slots();
    // แผงโควตาเข้า/ออกตามลิงก์ และนาฬิกาใหญ่ต้องกลับลงมายึดพื้นที่ที่มันปล่อยไว้
    layout_cards();
    layout_usage();
    layout_machine();
    layout_usage_topbar();
    for (int i = 0; i < PCH_SLOTS_COUNT; i++) lv_obj_invalidate(s_slots[i].canvas);
    lv_obj_invalidate(s_stroll);
}

// นาฬิกาใหญ่อยู่คนละที่ในสองโหมด
//
// ตอนกลางวันมันเป็นผู้เช่าชั่วคราวของพื้นที่ที่การ์ดกับแผงโควตาจะมายึดคืนเมื่อไรก็ได้
// จึงต้องนั่งตรงกลาง *ของพื้นที่นั้น* ไม่ใช่ของจอ ไม่งั้นพอการ์ดโผล่มามันจะทับกัน
//
// ตอนกลางคืนไม่มีใครมาแย่ง ทั้งจอเป็นของมัน — การยังนั่งค่อนล่างเหมือนเดิมจึงอ่านเป็น
// "วางผิดที่" ไม่ใช่ "เว้นที่ไว้ให้คนอื่น" เพราะไม่มีคนอื่นให้เห็นแล้ว
static void place_idle_clock(void)
{
    if (s_night) {
        int bottom = PCH_TOPBAR_HEIGHT + (PCH_SCREEN_HEIGHT - PCH_TOPBAR_HEIGHT - BC_H) / 2 - 12
                     + BC_H;
        lv_obj_align(s_date, LV_ALIGN_TOP_MID, 0, bottom + 12);
        return;
    }
    lv_obj_align(s_clock_big, LV_ALIGN_TOP_MID, 0, PCH_CARD_TOP + PCH_CARD_HEIGHT / 2 - 32);
    lv_obj_align(s_date, LV_ALIGN_TOP_MID, 0, PCH_CARD_TOP + PCH_CARD_HEIGHT / 2 + 18);
}

void pch_ui_set_night(bool on)
{
    if (on == s_night) return;
    s_night = on;
    place_idle_clock();
    update_sky();  // ผืนใหญ่สลับหน้าที่ระหว่างฉากกับนาฬิกา ต้องวาดใหม่ทันที
    // เข้าหรือออกโหมดนี้เปลี่ยนทุกอย่างที่แย่งพื้นที่กัน จึงต้องจัดใหม่ทั้งชุด
    // ไม่ใช่ซ่อนทีละชิ้น — นาฬิกาใหญ่โผล่เองเมื่อไม่มีใครยึดพื้นที่ล่าง ซึ่งเป็นทางเดียว
    // กับตอนไม่มี session ที่มีอยู่แล้ว
    layout_slots();
    layout_cards();
    layout_usage();
    layout_machine();
    layout_usage_topbar();
}

void pch_ui_peek_usage(void)
{
    // ไม่มีโควตาให้ดูก็ไม่ต้องทำอะไร — การซ่อนการ์ดทิ้งเพื่อโชว์ที่ว่างคือการลงโทษคนแตะ
    if (!usage_shown()) return;
    bool was_off = s_peek_ms == 0;
    s_peek_ms = PCH_PEEK_MS;
    // แตะซ้ำระหว่างที่ยังโชว์อยู่ = ต่อเวลา ไม่ใช่วาดใหม่ทั้งจอ
    if (!was_off) return;
    layout_cards();
    layout_usage();
    layout_machine();
    layout_usage_topbar();
}

void pch_ui_tick(void)
{
    if (s_peek_ms > 0) {
        s_peek_ms -= FRAME_MS;
        if (s_peek_ms <= 0) {
            s_peek_ms = 0;
            layout_cards();
            layout_usage();
            layout_machine();
            layout_usage_topbar();
        }
    }
    s_phase += (float)FRAME_MS / (float)LOOP_MS;
    bool second_passed = false;
    while (s_phase >= 1.0f) {
        s_phase -= 1.0f;
        s_cycle++;
        second_passed = true;
    }
    for (int i = 0; i < s_snap.session_count; i++) {
        lv_obj_invalidate(s_slots[i].canvas);
    }
    if (s_snap.session_count == 0) lv_obj_invalidate(s_stroll);

    // ฟ้าวาดใหม่ตอนเมฆขยับถึงพิกเซลถัดไป (~4 ครั้ง/วิ) หรือตอนวินาทีเดิน (ดาวกะพริบ)
    // ไม่ใช่ทุกเฟรม — ที่ 60ms ต่อเฟรมจะได้ 16 ครั้ง/วิ โดยที่ภาพเปลี่ยนแค่ 4 ครั้ง
    if (s_sky_phase != PCH_SKY_NONE) {
        int shift = (int)(((float)s_cycle + s_phase) * (float)PCH_SKY_CLOUD_SPEED_PX_S);
        // ฝนวิ่ง 150px/วิ ถ้าใช้เกตของเมฆ (4px/วิ) จะเห็นเป็นภาพนิ่งกระตุก
        // ฟ้าแลบก็สั้นกว่าคาบของเกตเดิม จึงต้องวาดทุกเฟรมตอนมีอากาศเคลื่อนไหว
        bool animated = weather_is_wet() || (s_snap.has_weather
                                             && s_snap.weather == PCH_WEATHER_STORM);
        if (shift != s_cloud_shift || second_passed || animated) {
            s_cloud_shift = shift;
            invalidate_sky_band();
        }
    }

    // countdown เดินด้วยนาฬิกาของบอร์ดเอง ไม่ใช่ snapshot — เวลารีเซ็ตเป็นค่าสัมบูรณ์
    // BLE หลุดแล้วตัวเลขนี้ยังจริง ส่วนเปอร์เซ็นต์หยุดนิ่ง (ซึ่งถูก มันหยุดจริง)
    //
    // วาดใหม่เฉพาะตอนวินาทีเดิน และเฉพาะตอนแผงโผล่อยู่ — LVGL วาดเฉพาะสิ่งที่
    // invalidate เท่านั้น การเรียก layout_usage ทุกเฟรมจะกินเวลาไปเปล่าๆ
    // ตอนหลุดลิงก์ countdown ยังเดินในหน่วยความจำ (ค่าที่ถูกตอนกลับมาต่อ) แต่ไม่มีอะไรให้วาด
    if (second_passed && s_snap.has_usage) {
        pch_model_tick_usage(&s_snap, 1);
        if (usage_shown()) {
            if (shown_card_count() == 0) {
                layout_usage();
                layout_machine();
            } else {
                layout_usage_topbar();
            }
        }
    }
}
